NollKollTroll/PZ1_Pico/pico_sw/6502-src/ehbasic.asm

//Enhanced BASIC ver 2.22p5.7ak
// 2.00      new revision numbers start here
// 2.01      fixed LCASE$() and UCASE$()
// 2.02      new get value routine done
// 2.03      changed RND() to galoise method
// 2.04      fixed SPC()
// 2.05      new get value routine fixed
// 2.06      changed USR() code
// 2.07      fixed STR$()
// 2.08      changed INPUT and READ to remove need for $00 start to input buffer
// 2.09      fixed RND()
// 2.10      integrated missed changes from an earlier version
// 2.20      added ELSE to IF .. THEN and fixed IF .. GOTO <statement> to cause error
// 2.21      fixed IF .. THEN RETURN to not cause error
// 2.22      fixed RND() breaking the get byte routine
// 2.22p     patched to disable use of decimal mode and fix Ibuff issues
//              (bugsnquirks.txt notes 2, 4 and 5)
//              tabs converted to spaces, tabwidth=6
// 2.22p2    fixed can't continue error on 1st statement after direct mode
//              changed INPUT to throw "break in line ##" on empty line input
// 2.22p3    fixed RAM above code / Ibuff above EhBASIC patch breaks STR$()
//              fix provided by github user mgcaret
// 2.22p4    fixed string compare of equal strings in direct mode returns FALSE
//              fixed FALSE stored to a variable after a string compare
//                 is > 0 and < 1E-16
//              added additional stack floor protection for background interrupts
//              fixed conditional LOOP & NEXT cannot find their data strucure on stack
// 2.22p5    fixes issues reported by users Ruud and dclxvi on the 6502.org forum
//      5.0     http://forum.6502.org/viewtopic.php?f=5&t=5500
//              sanity check for RAM top allows values below RAM base
//      5.1-7   http://forum.6502.org/viewtopic.php?f=5&t=5606
//              1-7 coresponds to the bug# in the thread
//      5.1     TO expression with a subtract may evaluate with the sign bit flipped
//      5.3     call to LAB_1B5B may return to an address -$100 (page not incremented)
//      5.4     string concatenate followed by MINUS or NOT() crashes EhBASIC
//      5.5     garbage collection may cause an overlap with temporary strings
//      5.6     floating point multiply rounding bug
//      5.7     VAL() may cause string variables to be trashed
// 2.22p5.7ak   Adam Klotblixt: PZ1 additions and changes, jasm-fixed.

include "portdefs.asm"
include "zpos.asm"
include "oscalls.asm"

section code, "dummy filler for ROM", 0, 512
{
    define byte[512] dummy_filler = {0, ...}
}

section bss, "zeropage basic", 0, 224
{
    // zero page use
    // the following locations are bulk initialized from StrTab at LAB_GMEM
    reserve byte LAB_WARM           // BASIC warm start entry point:
    reserve byte Wrmjpl             // BASIC warm start vector jump low byte
    reserve byte Wrmjph             // BASIC warm start vector jump high byte
    reserve byte Usrjmp             // USR function jmp address
    reserve byte Usrjpl             // USR function jmp vector low byte
    reserve byte Usrjph             // USR function jmp vector high byte
    reserve byte Nullct             // nulls output after each line
    reserve byte TPos               // BASIC terminal position byte
    reserve byte TWidth             // BASIC terminal width byte
    reserve byte Iclim              // input column limit
    reserve byte Itempl             // temporary integer low byte
    reserve byte Itemph             // temporary integer high byte
    // end bulk initialize from StrTab at LAB_GMEM

    const        nums_1  = Itempl   // number to bin/hex string convert MSB
    const        nums_2  = nums_1+1 // number to bin/hex string convert
    reserve byte nums_3             // number to bin/hex string convert LSB

    reserve byte Srchc              // search character
    const        Temp3   = Srchc    // temp byte used in number routines
    reserve byte Scnquo             // scan-between-quotes flag
    const        Asrch   = Scnquo   // alt search character

    const        XOAw_l  = Srchc    // XOR, OR and AND word low byte
    const        XOAw_h  = Scnquo   // XOR, OR and AND word high byte

    reserve byte Ibptr              // input buffer pointer
    const        Dimcnt  = Ibptr    // # of dimensions
    const        Tindx   = Ibptr    // token index

    reserve byte Defdim              // default DIM flag
    reserve byte Dtypef              // data type flag, $FF=string, $00=numeric
    reserve byte Oquote              // open quote flag (b7) (Flag: DATA scan// LIST quote// memory)
    const        Gclctd  = Oquote    // garbage collected flag
    reserve byte Sufnxf              // subscript/FNX flag, 1xxx xxx = FN(0xxx xxx)
    reserve byte Imode               // input mode flag, $00=INPUT, $80=READ

    reserve byte Cflag               // comparison evaluation flag

    reserve byte TabSiz              // TAB step size (was input flag)

    reserve byte next_s              // next descriptor stack address

    // these two bytes form a word pointer to the item
    // currently on top of the descriptor stack
    reserve byte last_sl             // last descriptor stack address low byte
    reserve byte last_sh             // last descriptor stack address high byte (always $00)

    reserve byte [9] des_sk          // descriptor stack start address (temp strings)

    reserve byte ut1_pl              // utility pointer 1 low byte
    reserve byte ut1_ph              // utility pointer 1 high byte
    reserve byte ut2_pl              // utility pointer 2 low byte
    reserve byte ut2_ph              // utility pointer 2 high byte

    const        Temp_2  = ut1_pl    // temp byte for block move

    reserve byte FACt_1              // FAC temp mantissa1
    reserve byte FACt_2              // FAC temp mantissa2
    reserve byte FACt_3              // FAC temp mantissa3

    const        dims_l  = FACt_2    // array dimension size low byte
    const        dims_h  = FACt_3    // array dimension size high byte

    reserve byte TempB               // temp page 0 byte

    reserve byte Smeml               // start of mem low byte       (Start-of-Basic)
    reserve byte Smemh               // start of mem high byte      (Start-of-Basic)
    reserve byte Svarl               // start of vars low byte      (Start-of-Variables)
    reserve byte Svarh               // start of vars high byte     (Start-of-Variables)
    reserve byte Sarryl              // var mem end low byte        (Start-of-Arrays)
    reserve byte Sarryh              // var mem end high byte       (Start-of-Arrays)
    reserve byte Earryl              // array mem end low byte      (End-of-Arrays)
    reserve byte Earryh              // array mem end high byte     (End-of-Arrays)
    reserve byte Sstorl              // string storage low byte     (String storage (moving down))
    reserve byte Sstorh              // string storage high byte    (String storage (moving down))
    reserve byte Sutill              // string utility ptr low byte
    reserve byte Sutilh              // string utility ptr high byte
    reserve byte Ememl               // end of mem low byte         (Limit-of-memory)
    reserve byte Ememh               // end of mem high byte        (Limit-of-memory)
    reserve byte Clinel              // current line low byte       (Basic line number)
    reserve byte Clineh              // current line high byte      (Basic line number)
    reserve byte Blinel              // break line low byte         (Previous Basic line number)
    reserve byte Blineh              // break line high byte        (Previous Basic line number)

    reserve byte Cpntrl              // continue pointer low byte
    reserve byte Cpntrh              // continue pointer high byte

    reserve byte Dlinel              // current DATA line low byte
    reserve byte Dlineh              // current DATA line high byte

    reserve byte Dptrl               // DATA pointer low byte
    reserve byte Dptrh               // DATA pointer high byte

    reserve byte Rdptrl              // read pointer low byte
    reserve byte Rdptrh              // read pointer high byte

    reserve byte Varnm1              // current var name 1st byte
    reserve byte Varnm2              // current var name 2nd byte

    reserve byte Cvaral              // current var address low byte
    reserve byte Cvarah              // current var address high byte

    reserve byte Frnxtl              // var pointer for FOR/NEXT low byte
    reserve byte Frnxth              // var pointer for FOR/NEXT high byte

    const        Tidx1   = Frnxtl    // temp line index

    const        Lvarpl  = Frnxtl    // let var pointer low byte
    const        Lvarph  = Frnxth    // let var pointer high byte

    reserve byte [2] prstk           // precedence stacked flag

    reserve byte comp_f              // compare function flag, bits 0,1 and 2 used
                                     // bit 2 set if >
                                     // bit 1 set if =
                                     // bit 0 set if <

    reserve byte func_l              // function pointer low byte
    reserve byte func_h              // function pointer high byte

    const        garb_l  = func_l    // garbage collection working pointer low byte
    const        garb_h  = func_h    // garbage collection working pointer high byte

    reserve byte des_2l              // string descriptor_2 pointer low byte
    reserve byte des_2h              // string descriptor_2 pointer high byte

    reserve byte g_step              // garbage collect step size

    reserve byte Fnxjmp              // jump vector for functions
    reserve byte Fnxjpl              // functions jump vector low byte
    reserve byte Fnxjph              // functions jump vector high byte

    const        g_indx  = Fnxjpl    // garbage collect temp index

    const        FAC2_r  = Fnxjph    // FAC2 rounding byte

    reserve byte Adatal              // array data pointer low byte
    reserve byte Adatah              // array data pointer high  byte

    const        Nbendl  = Adatal    // new block end pointer low byte
    const        Nbendh  = Adatah    // new block end pointer high  byte

    reserve byte Obendl              // old block end pointer low byte
    reserve byte Obendh              // old block end pointer high  byte

    reserve byte numexp              // string to float number exponent count
    reserve byte expcnt              // string to float exponent count

    const        numbit  = numexp    // bit count for array element calculations

    reserve byte numdpf              // string to float decimal point flag
    reserve byte expneg              // string to float eval exponent -ve flag

    const        Astrtl  = numdpf    // array start pointer low byte
    const        Astrth  = expneg    // array start pointer high  byte

    const        Histrl  = numdpf    // highest string low byte
    const        Histrh  = expneg    // highest string high  byte

    const        Baslnl  = numdpf    // BASIC search line pointer low byte
    const        Baslnh  = expneg    // BASIC search line pointer high  byte

    const        Fvar_l  = numdpf    // find/found variable pointer low byte
    const        Fvar_h  = expneg    // find/found variable pointer high  byte

    const        Ostrtl  = numdpf    // old block start pointer low byte
    const        Ostrth  = expneg    // old block start pointer high  byte

    const        Vrschl  = numdpf    // variable search pointer low byte
    const        Vrschh  = expneg    // variable search pointer high  byte

    reserve byte FAC1_e              // FAC1 exponent

    reserve byte FAC1_1              // FAC1 mantissa1
    reserve byte FAC1_2              // FAC1 mantissa2
    reserve byte FAC1_3              // FAC1 mantissa3
    reserve byte FAC1_s              // FAC1 sign (b7)

    const        str_ln  = FAC1_e    // string length
    const        str_pl  = FAC1_1    // string pointer low byte
    const        str_ph  = FAC1_2    // string pointer high byte

    const        des_pl  = FAC1_2    // string descriptor pointer low byte
    const        des_ph  = FAC1_3    // string descriptor pointer high byte

    const        mids_l  = FAC1_3    // MID$ string temp length byte

    reserve byte negnum              // string to float eval -ve flag
    const        numcon  = negnum    // series evaluation constant count

    reserve byte FAC1_o              // FAC1 overflow byte

    reserve byte FAC2_e              // FAC2 exponent
    reserve byte FAC2_1              // FAC2 mantissa1
    reserve byte FAC2_2              // FAC2 mantissa2
    reserve byte FAC2_3              // FAC2 mantissa3
    reserve byte FAC2_s              // FAC2 sign (b7)

    reserve byte FAC_sc              // FAC sign comparison, Acc#1 vs #2
    reserve byte FAC1_r              // FAC1 rounding byte

    const        ssptr_l = FAC_sc    // string start pointer low byte
    const        ssptr_h = FAC1_r    // string start pointer high byte

    const        sdescr  = FAC_sc    // string descriptor pointer

    reserve byte Asptl               // array size/pointer low byte
    reserve byte Aspth               // array size/pointer high byte

    const        csidx   = Asptl     // line crunch save index

    const        Btmpl   = Asptl     // BASIC pointer temp low byte
    const        Btmph   = Aspth     // BASIC pointer temp low byte

    const        Cptrl   = Asptl     // BASIC pointer temp low byte
    const        Cptrh   = Aspth     // BASIC pointer temp low byte

    const        Sendl   = Asptl     // BASIC pointer temp low byte
    const        Sendh   = Aspth     // BASIC pointer temp low byte

    // the following locations are bulk initialized from LAB_2CEE at LAB_2D4E
    reserve byte [6] LAB_IGBY        // get next BASIC byte subroutine:
    reserve byte LAB_GBYT            // get current BASIC byte subroutine:
    reserve byte Bpntrl              // BASIC execute (get byte) pointer low byte
    reserve byte Bpntrh              // BASIC execute (get byte) pointer high byte
    reserve byte [19];
    // end bulk initialize from LAB_2CEE at LAB_2D4E

    reserve byte Rbyte4              // extra PRNG byte
    reserve byte Rbyte1              // most significant PRNG byte
    reserve byte Rbyte2              // middle PRNG byte
    reserve byte Rbyte3              // least significant PRNG byte

    reserve byte Decss               // number to decimal string start
    reserve byte [16] Decssp1        // number to decimal string start
    
    // Ibuffs can now be anywhere in RAM, ensure that the max length is < $80,
    // the input buffer must not cross a page boundary and must not overlap with
    // program RAM pages!
    reserve byte [65] Ibuffs         // input buffer
}

section code, "basic code", $0200, 16384
{
BASIC_begin:
    // offsets from a base of x or y
    const PLUS_0            = $00             // x or y plus 0
    const PLUS_1            = $01             // x or y plus 1
    const PLUS_2            = $02             // x or y plus 2
    const PLUS_3            = $03             // x or y plus 3

    const LAB_STAK          = $0100           // stack bottom, no offset
    const LAB_SKFE          = LAB_STAK+$FE    // flushed stack address
    const LAB_SKFF          = LAB_STAK+$FF    // flushed stack address

    const Ram_base          = BASIC_end       // start of user RAM (set as needed, should be page aligned)
    const Ram_top           = $FE00           // end of user RAM+1 (set as needed, should be page aligned)

    static_assert((Ram_base & $ff) == 0, "Ram_base not page aligned")
    static_assert((Ram_top & $ff) == 0, "Ram_top not page aligned")

    const Stack_floor       = 16              // bytes left free on stack for background interrupts

    // BASIC cold start entry point
    LAB_COLD:
          ldx   #$FF              // set byte
          stx   Clineh            // set current line high byte (set immediate mode)
          txs                     // reset stack pointer

          lda   #$4C              // code for jmp
          sta   Fnxjmp            // save for jump vector for functions

    // copy block from LAB_2CEE to $00BC - $00D7
          ldx   #StrTab-LAB_2CEE  // set byte count
    LAB_2D4E:
          lda   LAB_2CEE-1,x      // get byte from table
          sta   LAB_IGBY-1,x      // save byte in page zero
          dex                     // decrement count
          bne   LAB_2D4E          // loop if not all done

    // copy block from StrTab to $0000 - $0012
    LAB_GMEM:
          ldx   #EndTab-StrTab-1  // set byte count-1
    TabLoop:
          lda   StrTab,x          // get byte from table
          sta   LAB_WARM,x        // save byte in page zero
          dex                     // decrement count
          bpl   TabLoop           // loop if not all done

    // set-up start values
          lda   #$00              // clear a
          sta   FAC1_o            // clear FAC1 overflow byte
          sta   last_sh           // clear descriptor stack top item pointer high byte

          lda   #$08              // set default tab size
          sta   TabSiz            // save it
          lda   #$03              // set garbage collect step size for descriptor stack
          sta   g_step            // save it
          ldx   #des_sk           // descriptor stack start
          stx   next_s            // set descriptor stack pointer
          lda   #<LAB_MSZM        // point to memory size message (low addr)
          ldy   #>LAB_MSZM        // point to memory size message (high addr)
          jsr   LAB_18C3          // print null terminated string from memory

    MEM_OK:
          lda   #<Ram_top         //BASIC_begin
          ldy   #>Ram_top         //BASIC_begin

          sta   Ememl             // set end of mem low byte
          sty   Ememh             // set end of mem high byte
          sta   Sstorl            // set bottom of string space low byte
          sty   Sstorh            // set bottom of string space high byte

          ldy   #<Ram_base        // set start addr low byte
          ldx   #>Ram_base        // set start addr high byte
          sty   Smeml             // save start of mem low byte
          stx   Smemh             // save start of mem high byte

          tya                     // clear a
          sta   (Smeml),y         // clear first byte
          inc   Smeml             // increment start of mem low byte

          jsr   LAB_1463          // do "NEW" and "CLEAR"
          lda   Ememl             // get end of mem low byte
          sec                     // set carry for subtract
          sbc   Smeml             // subtract start of mem low byte
          tax                     // copy to x
          lda   Ememh             // get end of mem high byte
          sbc   Smemh             // subtract start of mem high byte
          jsr   LAB_295E          // print XA as unsigned integer (bytes free)
          lda   #<LAB_SMSG        // point to sign-on message (low addr)
          ldy   #>LAB_SMSG        // point to sign-on message (high addr)
          jsr   LAB_18C3          // print null terminated string from memory
          lda   #<LAB_COPY        // point to copyright message (low addr)
          ldy   #>LAB_COPY        // point to copyright message (high addr)
          jsr   LAB_18C3          // print null terminated string from memory
          lda   #<LAB_1274        // warm start vector low byte
          ldy   #>LAB_1274        // warm start vector high byte
          sta   Wrmjpl            // save warm start vector low byte
          sty   Wrmjph            // save warm start vector high byte
          jmp   (Wrmjpl)          // go do warm start

    // open up space in memory
    // move (Ostrtl)-(Obendl) to new block ending at (Nbendl)

    // Nbendl,Nbendh - new block end address (a/y)
    // Obendl,Obendh - old block end address
    // Ostrtl,Ostrth - old block start address

    // returns with ..

    // Nbendl,Nbendh - new block start address (high byte - $100)
    // Obendl,Obendh - old block start address (high byte - $100)
    // Ostrtl,Ostrth - old block start address (unchanged)

    LAB_11CF:
          jsr   LAB_121F          // check available memory, "Out of memory" error if no room
                                  // addr to check is in AY (low/high)
          sta   Earryl            // save new array mem end low byte
          sty   Earryh            // save new array mem end high byte

    // open up space in memory
    // move (Ostrtl)-(Obendl) to new block ending at (Nbendl)
    // don't set array end

    LAB_11D6:
          sec                     // set carry for subtract
          lda   Obendl            // get block end low byte
          sbc   Ostrtl            // subtract block start low byte
          tay                     // copy MOD(block length/$100) byte to y
          lda   Obendh            // get block end high byte
          sbc   Ostrth            // subtract block start high byte
          tax                     // copy block length high byte to x
          inx                     // +1 to allow for count=0 exit
          tya                     // copy block length low byte to a
          beq   LAB_120A          // branch if length low byte=0

                                  // block is (x-1)*256+y bytes, do the y bytes first

          sec                     // set carry for add + 1, two's complement
          eor   #$FF              // invert low byte for subtract
          adc   Obendl            // add block end low byte

          sta   Obendl            // save corrected old block end low byte
          bcs   LAB_11F3          // branch if no underflow

          dec   Obendh            // else decrement block end high byte
          sec                     // set carry for add + 1, two's complement
    LAB_11F3:
          tya                     // get MOD(block length/$100) byte
          eor   #$FF              // invert low byte for subtract
          adc   Nbendl            // add destination end low byte
          sta   Nbendl            // save modified new block end low byte
          bcs   LAB_1203          // branch if no underflow

          dec   Nbendh            // else decrement block end high byte
          bcc   LAB_1203          // branch always

    LAB_11FF:
          lda   (Obendl),y        // get byte from source
          sta   (Nbendl),y        // copy byte to destination
    LAB_1203:
          dey                     // decrement index
          bne   LAB_11FF          // loop until y=0

                                  // now do y=0 indexed byte
          lda   (Obendl),y        // get byte from source
          sta   (Nbendl),y        // save byte to destination
    LAB_120A:
          dec   Obendh            // decrement source pointer high byte
          dec   Nbendh            // decrement destination pointer high byte
          dex                     // decrement block count
          bne   LAB_1203          // loop until count = $0

          rts

    // check room on stack for a bytes
    // stack too deep? do OM error

    LAB_1212:
    // *** patch - additional stack floor protection for background interrupts
    // *** add
          if (Stack_floor != 0)
          {
              clc                     // prep adc
              adc   #Stack_floor      // stack pointer lower limit before interrupts
          }
    // *** end patch
          sta   TempB             // save result in temp byte
          tsx                     // copy stack
          cpx   TempB             // compare new "limit" with stack
          bcc   LAB_OMER          // if stack < limit do "Out of memory" error then warm start

          rts

    // check available memory, "Out of memory" error if no room
    // addr to check is in AY (low/high)

    LAB_121F:
          cpy   Sstorh            // compare bottom of string mem high byte
          bcc   LAB_124B          // if less then exit (is ok)

          bne   LAB_1229          // skip next test if greater (tested <)

                                  // high byte was =, now do low byte
          cmp   Sstorl            // compare with bottom of string mem low byte
          bcc   LAB_124B          // if less then exit (is ok)

                                  // addr is > string storage ptr (oops!)
    LAB_1229:
          pha                     // push addr low byte
          ldx   #$08              // set index to save Adatal to expneg inclusive
          tya                     // copy addr high byte (to push on stack)

                                  // save misc numeric work area
    LAB_122D:
          pha                     // push byte
          lda   Adatal-1,x        // get byte from Adatal to expneg ( ,$00 not pushed)
          dex                     // decrement index
          bpl   LAB_122D          // loop until all done

          jsr   LAB_GARB          // garbage collection routine

                                  // restore misc numeric work area
          ldx   #$00              // clear the index to restore bytes
    LAB_1238:
          pla                     // pop byte
          sta   Adatal,x          // save byte to Adatal to expneg
          inx                     // increment index
          cpx   #$08              // compare with end + 1
          bmi   LAB_1238          // loop if more to do

          pla                     // pop addr high byte
          tay                     // copy back to y
          pla                     // pop addr low byte
          cpy   Sstorh            // compare bottom of string mem high byte
          bcc   LAB_124B          // if less then exit (is ok)

          bne   LAB_OMER          // if greater do "Out of memory" error then warm start

                                  // high byte was =, now do low byte
          cmp   Sstorl            // compare with bottom of string mem low byte
          bcs   LAB_OMER          // if >= do "Out of memory" error then warm start

                                  // ok exit, carry clear
    LAB_124B:
          rts

    // do "Out of memory" error then warm start

    LAB_OMER:
          ldx   #$0C              // error code $0C ("Out of memory" error)

    // do error #x, then warm start

    LAB_XERR:
          jsr   LAB_CRLF          // print CR/LF

          lda   LAB_BAER,x        // get error message pointer low byte
          ldy   LAB_BAER+1,x      // get error message pointer high byte
          jsr   LAB_18C3          // print null terminated string from memory

          jsr   LAB_1491          // flush stack and clear continue flag
          lda   #<LAB_EMSG        // point to " Error" low addr
          ldy   #>LAB_EMSG        // point to " Error" high addr
    LAB_1269:
          jsr   LAB_18C3          // print null terminated string from memory
          ldy   Clineh            // get current line high byte
          iny                     // increment it
          beq   LAB_1274          // go do warm start (was immediate mode)

                                  // else print line number
          jsr   LAB_2953          // print " in line [LINE #]"

    // BASIC warm start entry point
    // wait for Basic command

    LAB_1274:
          lda   #<LAB_RMSG        // point to "Ready" message low byte
          ldy   #>LAB_RMSG        // point to "Ready" message high byte

          jsr   LAB_18C3          // go do print string

    // wait for Basic command (no "Ready")

    LAB_127D:
          jsr   LAB_1357          // call for BASIC input
    LAB_1280:
          stx   Bpntrl            // set BASIC execute pointer low byte
          sty   Bpntrh            // set BASIC execute pointer high byte
          jsr   LAB_GBYT          // scan memory
          beq   LAB_127D          // loop while null

    // got to interpret input line now ..

          ldx   #$FF              // current line to null value
          stx   Clineh            // set current line high byte
          bcc   LAB_1295          // branch if numeric character (handle new BASIC line)

                                  // no line number .. immediate mode
          jsr   LAB_13A6          // crunch keywords into Basic tokens
          jmp   LAB_15F6          // go scan and interpret code

    // handle new BASIC line

    LAB_1295:
          jsr   LAB_GFPN          // get fixed-point number into temp integer
          jsr   LAB_13A6          // crunch keywords into Basic tokens
          sty   Ibptr             // save index pointer to end of crunched line
          jsr   LAB_SSLN          // search BASIC for temp integer line number
          bcc   LAB_12E6          // branch if not found

                                  // aroooogah! line # already exists! delete it
          ldy   #$01              // set index to next line pointer high byte
          lda   (Baslnl),y        // get next line pointer high byte
          sta   ut1_ph            // save it
          lda   Svarl             // get start of vars low byte
          sta   ut1_pl            // save it
          lda   Baslnh            // get found line pointer high byte
          sta   ut2_ph            // save it
          lda   Baslnl            // get found line pointer low byte
          dey                     // decrement index
          sbc   (Baslnl),y        // subtract next line pointer low byte
          clc                     // clear carry for add
          adc   Svarl             // add start of vars low byte
          sta   Svarl             // save new start of vars low byte
          sta   ut2_pl            // save destination pointer low byte
          lda   Svarh             // get start of vars high byte
          adc   #$FF              // -1 + carry
          sta   Svarh             // save start of vars high byte
          sbc   Baslnh            // subtract found line pointer high byte
          tax                     // copy to block count
          sec                     // set carry for subtract
          lda   Baslnl            // get found line pointer low byte
          sbc   Svarl             // subtract start of vars low byte
          tay                     // copy to bytes in first block count
          bcs   LAB_12D0          // branch if overflow

          inx                     // increment block count (correct for =0 loop exit)
          dec   ut2_ph            // decrement destination high byte
    LAB_12D0:
          clc                     // clear carry for add
          adc   ut1_pl            // add source pointer low byte
          bcc   LAB_12D8          // branch if no overflow

          dec   ut1_ph            // else decrement source pointer high byte
          clc                     // clear carry

                                  // close up memory to delete old line
    LAB_12D8:
          lda   (ut1_pl),y        // get byte from source
          sta   (ut2_pl),y        // copy to destination
          iny                     // increment index
          bne   LAB_12D8          // while <> 0 do this block

          inc   ut1_ph            // increment source pointer high byte
          inc   ut2_ph            // increment destination pointer high byte
          dex                     // decrement block count
          bne   LAB_12D8          // loop until all done

                                  // got new line in buffer and no existing same #
    LAB_12E6:
          lda   Ibuffs            // get byte from start of input buffer
          beq   LAB_1319          // if null line just go flush stack/vars and exit

                                  // got new line and it isn't empty line
          lda   Ememl             // get end of mem low byte
          ldy   Ememh             // get end of mem high byte
          sta   Sstorl            // set bottom of string space low byte
          sty   Sstorh            // set bottom of string space high byte
          lda   Svarl             // get start of vars low byte  (end of BASIC)
          sta   Obendl            // save old block end low byte
          ldy   Svarh             // get start of vars high byte (end of BASIC)
          sty   Obendh            // save old block end high byte
          adc   Ibptr             // add input buffer pointer    (also buffer length)
          bcc   LAB_1301          // branch if no overflow from add

          iny                     // else increment high byte
    LAB_1301:
          sta   Nbendl            // save new block end low byte (move to, low byte)
          sty   Nbendh            // save new block end high byte
          jsr   LAB_11CF          // open up space in memory
                                  // old start pointer Ostrtl,Ostrth set by the find line call
          lda   Earryl            // get array mem end low byte
          ldy   Earryh            // get array mem end high byte
          sta   Svarl             // save start of vars low byte
          sty   Svarh             // save start of vars high byte
          ldy   Ibptr             // get input buffer pointer    (also buffer length)
          dey                     // adjust for loop type
    LAB_1311:
          lda   Ibuffs-4,y        // get byte from crunched line
          sta   (Baslnl),y        // save it to program memory
          dey                     // decrement count
          cpy   #$03              // compare with first byte-1
          bne   LAB_1311          // continue while count <> 3

          lda   Itemph            // get line # high byte
          sta   (Baslnl),y        // save it to program memory
          dey                     // decrement count
          lda   Itempl            // get line # low byte
          sta   (Baslnl),y        // save it to program memory
          dey                     // decrement count
          lda   #$FF              // set byte to allow chain rebuild. if you didn't set this
                                  // byte then a zero already here would stop the chain rebuild
                                  // as it would think it was the [EOT] marker.
          sta   (Baslnl),y        // save it to program memory

    LAB_1319:
          jsr   LAB_1477          // reset execution to start, clear vars and flush stack
          ldx   Smeml             // get start of mem low byte
          lda   Smemh             // get start of mem high byte
          ldy   #$01              // index to high byte of next line pointer
    LAB_1325:
          stx   ut1_pl            // set line start pointer low byte
          sta   ut1_ph            // set line start pointer high byte
          lda   (ut1_pl),y        // get it
          beq   LAB_133E          // exit if end of program

    // rebuild chaining of Basic lines

          ldy   #$04              // point to first code byte of line
                                  // there is always 1 byte + [EOL] as null entries are deleted
    LAB_1330:
          iny                     // next code byte
          lda   (ut1_pl),y        // get byte
          bne   LAB_1330          // loop if not [EOL]

          sec                     // set carry for add + 1
          tya                     // copy end index
          adc   ut1_pl            // add to line start pointer low byte
          tax                     // copy to x
          ldy   #$00              // clear index, point to this line's next line pointer
          sta   (ut1_pl),y        // set next line pointer low byte
          tya                     // clear a
          adc   ut1_ph            // add line start pointer high byte + carry
          iny                     // increment index to high byte
          sta   (ut1_pl),y        // save next line pointer low byte
          bcc   LAB_1325          // go do next line, branch always, carry clear


    LAB_133E:
          jmp   LAB_127D          // else we just wait for Basic command, no "Ready"

    // print "? " and get BASIC input

    LAB_INLN:
          jsr   LAB_18E3          // print "?" character
          jsr   LAB_18E0          // print " "
          bne   LAB_1357          // call for BASIC input and return

    // receive line from keyboard

                                  // $08 as delete key (BACKSPACE on standard keyboard)
    LAB_134B:
          jsr   LAB_PRNA          // go print the character
          dex                     // decrement the buffer counter (delete)
          define byte = $2C       // make ldx into bit abs

    // call for BASIC input (main entry point)

    LAB_1357:
          ldx   #$00              // clear BASIC line buffer pointer
    LAB_1359:
          jsr   V_INPT            // call scan input device
          bcc   LAB_1359          // loop if no byte

          beq   LAB_1359          // loop until valid input (ignore NULLs)
    
          cmp   #$07              // compare with [BELL]
          beq   LAB_1378          // branch if [BELL]

          cmp   #$0D              // compare with [CR]
          beq   LAB_1384          // do CR/LF exit if [CR]

          cpx   #$00              // compare pointer with $00
          bne   LAB_1374          // branch if not empty

    // next two lines ignore any non print character and [SPACE] if input buffer empty

          cmp   #$21              // compare with [SP]+1
          bcc   LAB_1359          // if < ignore character

    LAB_1374:
          cmp   #$08              // compare with [BACKSPACE] (delete last character)
          beq   LAB_134B          // go delete last character

    LAB_1378:
          cpx   #sizeof(Ibuffs)   // compare character count with max
          bcs   LAB_138E          // skip store and do [BELL] if buffer full

          sta   Ibuffs,x          // else store in buffer
          inx                     // increment pointer
    LAB_137F:
          jsr   LAB_PRNA          // go print the character
          bne   LAB_1359          // always loop for next character

    LAB_1384:
          jmp   LAB_1866          // do CR/LF exit to BASIC

    // announce buffer full

    LAB_138E:
          lda   #$07              // [BELL] character into a
          bne   LAB_137F          // go print the [BELL] but ignore input character
                                  // branch always

    // crunch keywords into Basic tokens
    // position independent buffer version ..
    // faster, dictionary search version ....

    LAB_13A6:
          ldy   #$FF              // set save index (makes for easy math later)

          sec                     // set carry for subtract
          lda   Bpntrl            // get basic execute pointer low byte
          sbc   #<Ibuffs          // subtract input buffer start pointer
          tax                     // copy result to x (index past line # if any)

          stx   Oquote            // clear open quote/DATA flag
    LAB_13AC:
          lda   Ibuffs,x          // get byte from input buffer
          beq   LAB_13EC          // if null save byte then exit
// *** patch
          cmp   #'{'              // convert lower to upper case
          bcs   LAB_13EC          // is above lower case
          cmp   #'a'
          bcc   PATCH_LC          // is below lower case
          and   #$DF              // mask lower case bit      
    PATCH_LC:
// *** end
          cmp   #'_'              // compare with "_"
          bcs   LAB_13EC          // if >= go save byte then continue crunching

          cmp   #'<'              // compare with "<"
          bcs   LAB_13CC          // if >= go crunch now

          cmp   #'0'              // compare with "0"
          bcs   LAB_13EC          // if >= go save byte then continue crunching

          sta   Scnquo            // save buffer byte as search character
          cmp   #$22              // is it quote character?
          beq   LAB_1410          // branch if so (copy quoted string)

          cmp   #'*'              // compare with "*"
          bcc   LAB_13EC          // if < go save byte then continue crunching

                                  // else crunch now
    LAB_13CC:
          bit   Oquote            // get open quote/DATA token flag
          bvs   LAB_13EC          // branch if b6 of Oquote set (was DATA)
                                  // go save byte then continue crunching

          stx   TempB             // save buffer read index
          sty   csidx             // copy buffer save index
          ldy   #<TAB_1STC        // get keyword first character table low address
          sty   ut2_pl            // save pointer low byte
          ldy   #>TAB_1STC        // get keyword first character table high address
          sty   ut2_ph            // save pointer high byte
          ldy   #$00              // clear table pointer

    LAB_13D0:
          cmp   (ut2_pl),y        // compare with keyword first character table byte
          beq   LAB_13D1          // go do word_table_chr if match

//          bcc   LAB_13EA          // if < keyword first character table byte go restore
// *** patch
          bcc   PATCH_LC2          // if < keyword first character table byte go restore
// *** end    
                                  // y and save to crunched

          iny                     // else increment pointer
          bne   LAB_13D0          // and loop (branch always)

    // have matched first character of some keyword

    LAB_13D1:
          tya                     // copy matching index
          asl                     // *2 (bytes per pointer)
          tax                     // copy to new index
          lda   TAB_CHRT,x        // get keyword table pointer low byte
          sta   ut2_pl            // save pointer low byte
          lda   TAB_CHRT+1,x      // get keyword table pointer high byte
          sta   ut2_ph            // save pointer high byte

          ldy   #$FF              // clear table pointer (make -1 for start)

          ldx   TempB             // restore buffer read index

    LAB_13D6:
          iny                     // next table byte
          lda   (ut2_pl),y        // get byte from table
    LAB_13D8:
          bmi   LAB_13EA          // all bytes matched so go save token

          inx                     // next buffer byte
//          cmp   Ibuffs,x          // compare with byte from input buffer
// *** patch
          eor     Ibuffs,x        // check bits against table
          and     #$DF            // DF masks the upper/lower case bit
// *** end    
          beq   LAB_13D6          // go compare next if match

          bne   LAB_1417          // branch if >< (not found keyword)

    LAB_13EA:
          ldy   csidx             // restore save index

                                  // save crunched to output
    LAB_13EC:
          inx                     // increment buffer index (to next input byte)
          iny                     // increment save index (to next output byte)
          sta   Ibuffs,y          // save byte to output
          cmp   #$00              // set the flags, set carry
          beq   LAB_142A          // do exit if was null [EOL]

                                  // a holds token or byte here
          sbc   #':'              // subtract ":" (carry set by cmp #00)
          beq   LAB_13FF          // branch if it was ":" (is now $00)

                                  // a now holds token-$3A
          cmp   #TK_DATA-$3A      // compare with DATA token - $3A
          bne   LAB_1401          // branch if not DATA

                                  // token was : or DATA
    LAB_13FF:
          sta   Oquote            // save token-$3A (clear for ":", TK_DATA-$3A for DATA)
    LAB_1401:
          eor   #TK_REM-$3A       // effectively subtract REM token offset
          bne   LAB_13AC          // If wasn't REM then go crunch rest of line

          sta   Asrch             // else was REM so set search for [EOL]

                                  // loop for REM, "..." etc.
    LAB_1408:
          lda   Ibuffs,x          // get byte from input buffer
          beq   LAB_13EC          // branch if null [EOL]

          cmp   Asrch             // compare with stored character
          beq   LAB_13EC          // branch if match (end quote)

                                  // entry for copy string in quotes, don't crunch
    LAB_1410:
          iny                     // increment buffer save index
          sta   Ibuffs,y          // save byte to output
          inx                     // increment buffer read index
          bne   LAB_1408          // loop while <> 0 (should never be 0!)

                                  // not found keyword this go
    LAB_1417:
          ldx   TempB             // compare has failed, restore buffer index (start byte!)

                                  // now find the end of this word in the table
    LAB_141B:
          lda   (ut2_pl),y        // get table byte
          php                     // save status
          iny                     // increment table index
          plp                     // restore byte status
          bpl   LAB_141B          // if not end of keyword go do next

          lda   (ut2_pl),y        // get byte from keyword table
          bne   LAB_13D8          // go test next word if not zero byte (end of table)

                                  // reached end of table with no match
// *** patch
    PATCH_LC2:
// *** end                                  
          lda   Ibuffs,x          // restore byte from input buffer
          bpl   LAB_13EA          // branch always (all bytes in buffer are $00-$7F)
                                  // go save byte in output and continue crunching

                                  // reached [EOL]
    LAB_142A:
          iny                     // increment pointer
          iny                     // increment pointer (makes it next line pointer high byte)
          sta   Ibuffs,y          // save [EOL] (marks [EOT] in immediate mode)
          iny                     // adjust for line copy
          iny                     // adjust for line copy
          iny                     // adjust for line copy
    // *** begin patch for when Ibuffs is $xx00 - Daryl Rictor ***
    // *** insert
          if (Ibuffs & $FF == 0)
          {
              lda   Bpntrl            // test for $00
              bne   LAB_142P          // not $00
              dec   Bpntrh            // allow for increment when $xx00
          LAB_142P:
          }
    // *** end   patch for when Ibuffs is $xx00 - Daryl Rictor ***
    // end of patch
          dec   Bpntrl            // allow for increment
          rts

    // search Basic for temp integer line number from start of mem

    LAB_SSLN:
          lda   Smeml             // get start of mem low byte
          ldx   Smemh             // get start of mem high byte

    // search Basic for temp integer line number from AX
    // returns carry set if found
    // returns Baslnl/Baslnh pointer to found or next higher (not found) line

    // old 541 new 507

    LAB_SHLN:
          ldy   #$01              // set index
          sta   Baslnl            // save low byte as current
          stx   Baslnh            // save high byte as current
          lda   (Baslnl),y        // get pointer high byte from addr
          beq   LAB_145F          // pointer was zero so we're done, do 'not found' exit

          ldy   #$03              // set index to line # high byte
          lda   (Baslnl),y        // get line # high byte
          dey                     // decrement index (point to low byte)
          cmp   Itemph            // compare with temporary integer high byte
          bne   LAB_1455          // if <> skip low byte check

          lda   (Baslnl),y        // get line # low byte
          cmp   Itempl            // compare with temporary integer low byte
    LAB_1455:
          bcs   LAB_145E          // else if temp < this line, exit (passed line#)

    LAB_1456:
          dey                     // decrement index to next line ptr high byte
          lda   (Baslnl),y        // get next line pointer high byte
          tax                     // copy to x
          dey                     // decrement index to next line ptr low byte
          lda   (Baslnl),y        // get next line pointer low byte
          bcc   LAB_SHLN          // go search for line # in temp (Itempl/Itemph) from AX
                                  // (carry always clear)

    LAB_145E:
          beq   LAB_1460          // exit if temp = found line #, carry is set

    LAB_145F:
          clc                     // clear found flag
    LAB_1460:
          rts

    // perform NEW

    LAB_NEW:
          bne   LAB_1460          // exit if not end of statement (to do syntax error)

    LAB_1463:
          lda   #$00              // clear a
          tay                     // clear y
          sta   (Smeml),y         // clear first line, next line pointer, low byte
          iny                     // increment index
          sta   (Smeml),y         // clear first line, next line pointer, high byte
          clc                     // clear carry
          lda   Smeml             // get start of mem low byte
          adc   #$02              // calculate end of BASIC low byte
          sta   Svarl             // save start of vars low byte
          lda   Smemh             // get start of mem high byte
          adc   #$00              // add any carry
          sta   Svarh             // save start of vars high byte

    // reset execution to start, clear vars and flush stack

    LAB_1477:
          clc                     // clear carry
          lda   Smeml             // get start of mem low byte
          adc   #$FF              // -1
          sta   Bpntrl            // save BASIC execute pointer low byte
          lda   Smemh             // get start of mem high byte
          adc   #$FF              // -1+carry
          sta   Bpntrh            // save BASIC execute pointer high byte

    // "CLEAR" command gets here

    LAB_147A:
          lda   Ememl             // get end of mem low byte
          ldy   Ememh             // get end of mem high byte
          sta   Sstorl            // set bottom of string space low byte
          sty   Sstorh            // set bottom of string space high byte
          lda   Svarl             // get start of vars low byte
          ldy   Svarh             // get start of vars high byte
          sta   Sarryl            // save var mem end low byte
          sty   Sarryh            // save var mem end high byte
          sta   Earryl            // save array mem end low byte
          sty   Earryh            // save array mem end high byte
          jsr   LAB_161A          // perform RESTORE command

    // flush stack and clear continue flag

    LAB_1491:
          ldx   #des_sk           // set descriptor stack pointer
          stx   next_s            // save descriptor stack pointer
          pla                     // pull return address low byte
          tax                     // copy return address low byte
          pla                     // pull return address high byte
          stx   LAB_SKFE          // save to cleared stack
          sta   LAB_SKFF          // save to cleared stack
          ldx   #$FD              // new stack pointer
          txs                     // reset stack
          lda   #$00              // clear byte
    //*** fix p2: no longer necessary as the continue pointer is saved anyway
    //      sta   Cpntrh            // clear continue pointer high byte
          sta   Sufnxf            // clear subscript/FNX flag
    LAB_14A6:
          rts

    // perform CLEAR

    LAB_CLEAR:
          beq   LAB_147A          // if no following token go do "CLEAR"

                                  // else there was a following token (go do syntax error)
          rts

    // perform LIST [n][-m]
    // bigger, faster version (a _lot_ faster)

    LAB_LIST:
          bcc   LAB_14BD          // branch if next character numeric (LIST n..)

          beq   LAB_14BD          // branch if next character [NULL] (LIST)

          cmp   #TK_MINUS         // compare with token for -
          bne   LAB_14A6          // exit if not - (LIST -m)

                                  // LIST [[n][-m]]
                                  // this bit sets the n , if present, as the start and end
    LAB_14BD:
          jsr   LAB_GFPN          // get fixed-point number into temp integer
          jsr   LAB_SSLN          // search BASIC for temp integer line number
                                  // (pointer in Baslnl/Baslnh)
          jsr   LAB_GBYT          // scan memory
          beq   LAB_14D4          // branch if no more characters

                                  // this bit checks the - is present
          cmp   #TK_MINUS         // compare with token for -
          bne   LAB_1460          // return if not "-" (will be Syntax error)

                                  // LIST [n]-m
                                  // the - was there so set m as the end value
          jsr   LAB_IGBY          // increment and scan memory
          jsr   LAB_GFPN          // get fixed-point number into temp integer
          bne   LAB_1460          // exit if not ok

    LAB_14D4:
          lda   Itempl            // get temporary integer low byte
          ora   Itemph            // OR temporary integer high byte
          bne   LAB_14E2          // branch if start set

          lda   #$FF              // set for -1
          sta   Itempl            // set temporary integer low byte
          sta   Itemph            // set temporary integer high byte
    LAB_14E2:
          ldy   #$01              // set index for line
          sty   Oquote            // clear open quote flag
          jsr   LAB_CRLF          // print CR/LF
          lda   (Baslnl),y        // get next line pointer high byte
                                  // pointer initially set by search at LAB_14BD
          beq   LAB_152B          // if null all done so exit
          jsr   LAB_1629          // do CRTL-C check vector

          iny                     // increment index for line
          lda   (Baslnl),y        // get line # low byte
          tax                     // copy to x
          iny                     // increment index
          lda   (Baslnl),y        // get line # high byte
          cmp   Itemph            // compare with temporary integer high byte
          bne   LAB_14FF          // branch if no high byte match

          cpx   Itempl            // compare with temporary integer low byte
          beq   LAB_1501          // branch if = last line to do (< will pass next branch)

    LAB_14FF:                     // else ..:
          bcs   LAB_152B          // if greater all done so exit

    LAB_1501:
          sty   Tidx1             // save index for line
          jsr   LAB_295E          // print XA as unsigned integer
          lda   #$20              // space is the next character
    LAB_1508:
          ldy   Tidx1             // get index for line
          and   #$7F              // mask top out bit of character
    LAB_150C:
          jsr   LAB_PRNA          // go print the character
          cmp   #$22              // was it " character
          bne   LAB_1519          // branch if not

                                  // we are either entering or leaving a pair of quotes
          lda   Oquote            // get open quote flag
          eor   #$FF              // toggle it
          sta   Oquote            // save it back
    LAB_1519:
          iny                     // increment index
          lda   (Baslnl),y        // get next byte
          bne   LAB_152E          // branch if not [EOL] (go print character)
          tay                     // else clear index
          lda   (Baslnl),y        // get next line pointer low byte
          tax                     // copy to x
          iny                     // increment index
          lda   (Baslnl),y        // get next line pointer high byte
          stx   Baslnl            // set pointer to line low byte
          sta   Baslnh            // set pointer to line high byte
          bne   LAB_14E2          // go do next line if not [EOT]
                                  // else ..
    LAB_152B:
          rts

    LAB_152E:
          bpl   LAB_150C          // just go print it if not token byte

                                  // else was token byte so uncrunch it (maybe)
          bit   Oquote            // test the open quote flag
          bmi   LAB_150C          // just go print character if open quote set

          ldx   #>LAB_KEYT        // get table address high byte
          asl                     // *2
          asl                     // *4
          bcc   LAB_152F          // branch if no carry

          inx                     // else increment high byte
          clc                     // clear carry for add
    LAB_152F:
          adc   #<LAB_KEYT        // add low byte
          bcc   LAB_1530          // branch if no carry

          inx                     // else increment high byte
    LAB_1530:
          sta   ut2_pl            // save table pointer low byte
          stx   ut2_ph            // save table pointer high byte
          sty   Tidx1             // save index for line
          ldy   #$00              // clear index
          lda   (ut2_pl),y        // get length
          tax                     // copy length
          iny                     // increment index
          lda   (ut2_pl),y        // get 1st character
          dex                     // decrement length
          beq   LAB_1508          // if no more characters exit and print

          jsr   LAB_PRNA          // go print the character
          iny                     // increment index
          lda   (ut2_pl),y        // get keyword address low byte
          pha                     // save it for now
          iny                     // increment index
          lda   (ut2_pl),y        // get keyword address high byte
          ldy   #$00
          sta   ut2_ph            // save keyword pointer high byte
          pla                     // pull low byte
          sta   ut2_pl            // save keyword pointer low byte
    LAB_1540:
          lda   (ut2_pl),y        // get character
          dex                     // decrement character count
          beq   LAB_1508          // if last character exit and print

          jsr   LAB_PRNA          // go print the character
          iny                     // increment index
          bne   LAB_1540          // loop for next character

    // perform FOR

    LAB_FOR:
          lda   #$80              // set FNX
          sta   Sufnxf            // set subscript/FNX flag
          jsr   LAB_LET           // go do LET
          pla                     // pull return address
          pla                     // pull return address
          lda   #$10              // we need 16d bytes !
          jsr   LAB_1212          // check room on stack for a bytes
          jsr   LAB_SNBS          // scan for next BASIC statement ([:] or [EOL])
          clc                     // clear carry for add
          tya                     // copy index to a
          adc   Bpntrl            // add BASIC execute pointer low byte
          pha                     // push onto stack
          lda   Bpntrh            // get BASIC execute pointer high byte
          adc   #$00              // add carry
          pha                     // push onto stack
          lda   Clineh            // get current line high byte
          pha                     // push onto stack
          lda   Clinel            // get current line low byte
          pha                     // push onto stack
          lda   #TK_TO            // get "TO" token
          jsr   LAB_SCCA          // scan for CHR$(a) , else do syntax error then warm start
          jsr   LAB_CTNM          // check if source is numeric, else do type mismatch
          jsr   LAB_EVNM          // evaluate expression and check is numeric,
                                  // else do type mismatch
    // *** begin patch  2.22p5.1   TO expression may get sign bit flipped
    // *** add
          jsr   LAB_27BA          // round FAC1
    // *** end   patch  2.22p5.1   TO expression may get sign bit flipped
          lda   FAC1_s            // get FAC1 sign (b7)
          ora   #$7F              // set all non sign bits
          and   FAC1_1            // and FAC1 mantissa1
          sta   FAC1_1            // save FAC1 mantissa1
          lda   #<LAB_159F        // set return address low byte
          ldy   #>LAB_159F        // set return address high byte
          sta   ut1_pl            // save return address low byte
          sty   ut1_ph            // save return address high byte
          jmp   LAB_1B66          // round FAC1 and put on stack (returns to next instruction)

    LAB_159F:
          lda   #<LAB_259C        // set 1 pointer low addr (default step size)
          ldy   #>LAB_259C        // set 1 pointer high addr
          jsr   LAB_UFAC          // unpack memory (AY) into FAC1
          jsr   LAB_GBYT          // scan memory
          cmp   #TK_STEP          // compare with STEP token
          bne   LAB_15B3          // jump if not "STEP"

                                  //.was step so ..
          jsr   LAB_IGBY          // increment and scan memory
          jsr   LAB_EVNM          // evaluate expression and check is numeric,
                                  // else do type mismatch
    LAB_15B3:
          jsr   LAB_27CA          // return a=FF,C=1/-ve a=01,C=0/+ve
          sta   FAC1_s            // set FAC1 sign (b7)
                                  // this is +1 for +ve step and -1 for -ve step, in NEXT we
                                  // compare the FOR value and the TO value and return +1 if
                                  // FOR > TO, 0 if FOR = TO and -1 if FOR < TO. the value
                                  // here (+/-1) is then compared to that result and if they
                                  // are the same (+ve and FOR > TO or -ve and FOR < TO) then
                                  // the loop is done

    // *** begin patch  2.22p5.3   potential return address -$100 (page not incremented) ***
    // *** add
       if ((* & $FF) == $FD)
       {
           nop                     // return address of jsr +1 (on  next page)
       }
    // *** end   patch  2.22p5.3   potential return address -$100 (page not incremented) ***
          jsr   LAB_1B5B          // push sign, round FAC1 and put on stack
          lda   Frnxth            // get var pointer for FOR/NEXT high byte
          pha                     // push on stack
          lda   Frnxtl            // get var pointer for FOR/NEXT low byte
          pha                     // push on stack
          lda   #TK_FOR           // get FOR token
          pha                     // push on stack

    // interpreter inner loop

    LAB_15C2:
          jsr   LAB_1629          // do CRTL-C check vector
          lda   Bpntrl            // get BASIC execute pointer low byte
          ldy   Bpntrh            // get BASIC execute pointer high byte

          ldx   Clineh            // continue line is $FFxx for immediate mode
                                  // ($00xx for RUN from immediate mode)
          inx                     // increment it (now $00 if immediate mode)
    //*** fix p2: skip no longer necessary as the continue pointer is saved anyway
    //      beq   LAB_15D1          // branch if null (immediate mode)

          sta   Cpntrl            // save continue pointer low byte
          sty   Cpntrh            // save continue pointer high byte
    LAB_15D1:
          ldy   #$00              // clear index
          lda   (Bpntrl),y        // get next byte
          beq   LAB_15DC          // branch if null [EOL]

          cmp   #':'              // compare with ":"
          beq   LAB_15F6          // branch if = (statement separator)

    LAB_15D9:
          jmp   LAB_SNER          // else syntax error then warm start

                                  // have reached [EOL]
    LAB_15DC:
          ldy   #$02              // set index
          lda   (Bpntrl),y        // get next line pointer high byte
          clc                     // clear carry for no "BREAK" message
          beq   LAB_1651          // if null go to immediate mode (was immediate or [EOT]
                                  // marker)

          iny                     // increment index
          lda   (Bpntrl),y        // get line # low byte
          sta   Clinel            // save current line low byte
          iny                     // increment index
          lda   (Bpntrl),y        // get line # high byte
          sta   Clineh            // save current line high byte
          tya                     // a now = 4
          adc   Bpntrl            // add BASIC execute pointer low byte
          sta   Bpntrl            // save BASIC execute pointer low byte
          bcc   LAB_15F6          // branch if no overflow

          inc   Bpntrh            // else increment BASIC execute pointer high byte
    LAB_15F6:
          jsr   LAB_IGBY          // increment and scan memory

    LAB_15F9:
          jsr   LAB_15FF          // go interpret BASIC code from (Bpntrl)

    LAB_15FC:
          jmp   LAB_15C2          // loop

    // interpret BASIC code from (Bpntrl)

    LAB_15FF:
          beq   LAB_1628          // exit if zero [EOL]

    LAB_1602:
          asl                     // *2 bytes per vector and normalise token
          bcs   LAB_1609          // branch if was token

          jmp   LAB_LET           // else go do implied LET

    LAB_1609:
          cmp   #(TK_TAB - $80) * 2 // compare normalised token * 2 with TAB
          bcs   LAB_15D9          // branch if a>=TAB (do syntax error then warm start)
                                  // only tokens before TAB can start a line
          tay                     // copy to index
          lda   LAB_CTBL+1,y      // get vector high byte
          pha                     // onto stack
          lda   LAB_CTBL,y        // get vector low byte
          pha                     // onto stack
          jmp   LAB_IGBY          // jump to increment and scan memory
                                  // then "return" to vector

    // CTRL-C check jump. this is called as a subroutine but exits back via a jump if a
    // key press is detected.

    LAB_1629:
          jmp   CTRLC             // ctrl c check vector

    // if there was a key press it gets back here ..

    LAB_1636:
          cmp   #$03              // compare with CTRL-C
          
    // perform STOP
    LAB_STOP:
          bcs   LAB_163B          // branch if token follows STOP
                                  // else just END
    // END
    LAB_END:
          clc                     // clear the carry, indicate a normal program end
    LAB_163B:
          bne   LAB_167A          // if wasn't CTRL-C or there is a following byte return

          lda   Bpntrh            // get the BASIC execute pointer high byte
    //*** fix p2: skip no longer necessary as the continue pointer is saved anyway
    //      eor   #>Ibuffs          // compare with buffer address high byte (Cb unchanged)
    //      beq   LAB_164F          // branch if the BASIC pointer is in the input buffer
    //                              // (can't continue in immediate mode)
    //                              // else ..
    //      eor   #>Ibuffs          // correct the bits
          ldy   Bpntrl            // get BASIC execute pointer low byte
          sty   Cpntrl            // save continue pointer low byte
          sta   Cpntrh            // save continue pointer high byte
    LAB_1647:
          lda   Clinel            // get current line low byte
          ldy   Clineh            // get current line high byte
          sta   Blinel            // save break line low byte
          sty   Blineh            // save break line high byte
    LAB_164F:
          pla                     // pull return address low
          pla                     // pull return address high
    LAB_1651:
          bcc   LAB_165E          // if was program end just do warm start

                                  // else ..
          lda   #<LAB_BMSG        // point to "Break" low byte
          ldy   #>LAB_BMSG        // point to "Break" high byte
          jmp   LAB_1269          // print "Break" and do warm start

    LAB_165E:
          jmp   LAB_1274          // go do warm start

    // perform RESTORE

    LAB_RESTORE:
          bne   LAB_RESTOREn      // branch if next character not null (RESTORE n)

    LAB_161A:
          sec                     // set carry for subtract
          lda   Smeml             // get start of mem low byte
          sbc   #$01              // -1
          ldy   Smemh             // get start of mem high byte
          bcs   LAB_1624          // branch if no underflow

    LAB_uflow:
          dey                     // else decrement high byte
    LAB_1624:
          sta   Dptrl             // save DATA pointer low byte
          sty   Dptrh             // save DATA pointer high byte
    LAB_1628:
          rts

                                  // is RESTORE n
    LAB_RESTOREn:
          jsr   LAB_GFPN          // get fixed-point number into temp integer
          jsr   LAB_SNBL          // scan for next BASIC line
          lda   Clineh            // get current line high byte
          cmp   Itemph            // compare with temporary integer high byte
          bcs   LAB_reset_search  // branch if >= (start search from beginning)

          tya                     // else copy line index to a
          sec                     // set carry (+1)
          adc   Bpntrl            // add BASIC execute pointer low byte
          ldx   Bpntrh            // get BASIC execute pointer high byte
          bcc   LAB_go_search     // branch if no overflow to high byte

          inx                     // increment high byte
          bcs   LAB_go_search     // branch always (can never be carry clear)

    // search for line # in temp (Itempl/Itemph) from start of mem pointer (Smeml)

    LAB_reset_search:
          lda   Smeml             // get start of mem low byte
          ldx   Smemh             // get start of mem high byte

    // search for line # in temp (Itempl/Itemph) from (AX)

    LAB_go_search:

          jsr   LAB_SHLN          // search Basic for temp integer line number from AX
          bcs   LAB_line_found    // if carry set go set pointer

          jmp   LAB_16F7          // else go do "Undefined statement" error

    LAB_line_found:
                                  // carry already set for subtract
          lda   Baslnl            // get pointer low byte
          sbc   #$01              // -1
          ldy   Baslnh            // get pointer high byte
          bcs   LAB_1624          // branch if no underflow (save DATA pointer and return)

          bcc   LAB_uflow         // else decrement high byte then save DATA pointer and
                                  // return (branch always)

    // perform NULL

    LAB_NULL:
          jsr   LAB_GTBY          // get byte parameter
          stx   Nullct            // save new NULL count
    LAB_167A:
          rts

    // perform CONT

    LAB_CONT:
          bne   LAB_167A          // if following byte exit to do syntax error

          ldy   Cpntrh            // get continue pointer high byte
          cpy   #>Ibuffs          // *** fix p2: test direct mode
          bne   LAB_166C          // go do continue if we can

          ldx   #$1E              // error code $1E ("Can't continue" error)
          jmp   LAB_XERR          // do error #x, then warm start

                                  // we can continue so ..
    LAB_166C:
          sty   Bpntrh            // save BASIC execute pointer high byte
          lda   Cpntrl            // get continue pointer low byte
          sta   Bpntrl            // save BASIC execute pointer low byte
          lda   Blinel            // get break line low byte
          ldy   Blineh            // get break line high byte
          sta   Clinel            // set current line low byte
          sty   Clineh            // set current line high byte
          rts

    // perform RUN

    LAB_RUN:
          bne   LAB_1696          // branch if RUN n
          jmp   LAB_1477          // reset execution to start, clear variables, flush stack and
                                  // return

    // does RUN n

    LAB_1696:
          jsr   LAB_147A          // go do "CLEAR"
          beq   LAB_16B0          // get n and do GOTO n (branch always as CLEAR sets Z=1)

    // perform DO

    LAB_DO:
          lda   #$05              // need 5 bytes for DO
          jsr   LAB_1212          // check room on stack for a bytes
          lda   Bpntrh            // get BASIC execute pointer high byte
          pha                     // push on stack
          lda   Bpntrl            // get BASIC execute pointer low byte
          pha                     // push on stack
          lda   Clineh            // get current line high byte
          pha                     // push on stack
          lda   Clinel            // get current line low byte
          pha                     // push on stack
          lda   #TK_DO            // token for DO
          pha                     // push on stack
          jsr   LAB_GBYT          // scan memory
          jmp   LAB_15C2          // go do interpreter inner loop

    // perform GOSUB

    LAB_GOSUB:
          lda   #$05              // need 5 bytes for GOSUB
          jsr   LAB_1212          // check room on stack for a bytes
          lda   Bpntrh            // get BASIC execute pointer high byte
          pha                     // push on stack
          lda   Bpntrl            // get BASIC execute pointer low byte
          pha                     // push on stack
          lda   Clineh            // get current line high byte
          pha                     // push on stack
          lda   Clinel            // get current line low byte
          pha                     // push on stack
          lda   #TK_GOSUB         // token for GOSUB
          pha                     // push on stack
    LAB_16B0:
          jsr   LAB_GBYT          // scan memory
          jsr   LAB_GOTO          // perform GOTO n
          jmp   LAB_15C2          // go do interpreter inner loop
                                  // (can't rts, we used the stack!)

    // perform GOTO

    LAB_GOTO:
          jsr   LAB_GFPN          // get fixed-point number into temp integer
          jsr   LAB_SNBL          // scan for next BASIC line
          lda   Clineh            // get current line high byte
          cmp   Itemph            // compare with temporary integer high byte
          bcs   LAB_16D0          // branch if >= (start search from beginning)

          tya                     // else copy line index to a
          sec                     // set carry (+1)
          adc   Bpntrl            // add BASIC execute pointer low byte
          ldx   Bpntrh            // get BASIC execute pointer high byte
          bcc   LAB_16D4          // branch if no overflow to high byte

          inx                     // increment high byte
          bcs   LAB_16D4          // branch always (can never be carry)

    // search for line # in temp (Itempl/Itemph) from start of mem pointer (Smeml)

    LAB_16D0:
          lda   Smeml             // get start of mem low byte
          ldx   Smemh             // get start of mem high byte

    // search for line # in temp (Itempl/Itemph) from (AX)

    LAB_16D4:
          jsr   LAB_SHLN          // search Basic for temp integer line number from AX
          bcc   LAB_16F7          // if carry clear go do "Undefined statement" error
                                  // (unspecified statement)

                                  // carry already set for subtract
          lda   Baslnl            // get pointer low byte
          sbc   #$01              // -1
          sta   Bpntrl            // save BASIC execute pointer low byte
          lda   Baslnh            // get pointer high byte
          sbc   #$00              // subtract carry
          sta   Bpntrh            // save BASIC execute pointer high byte
    LAB_16E5:
          rts

    LAB_DONOK:
          ldx   #$22              // error code $22 ("LOOP without DO" error)
          jmp   LAB_XERR          // do error #x, then warm start

    // perform LOOP

    LAB_LOOP:
          tay                     // save following token
          tsx                     // copy stack pointer
          lda   LAB_STAK+3,x      // get token byte from stack
          cmp   #TK_DO            // compare with DO token
          bne   LAB_DONOK         // branch if no matching DO

          inx                     // dump calling routine return address
          inx                     // dump calling routine return address
          txs                     // correct stack
          tya                     // get saved following token back
          beq   LoopAlways        // if no following token loop forever
                                  // (stack pointer in x)

          cmp   #':'              // could be ':'
          beq   LoopAlways        // if :... loop forever

          sbc   #TK_UNTIL         // subtract token for UNTIL, we know carry is set here
          tax                     // copy to x (if it was UNTIL then y will be correct)
          beq   DoRest            // branch if was UNTIL

          dex                     // decrement result
          bne   LAB_16FC          // if not WHILE go do syntax error and warm start
                                  // only if the token was WHILE will this fail

          dex                     // set invert result byte
    DoRest:
          stx   Frnxth            // save invert result byte
          jsr   LAB_IGBY          // increment and scan memory
          jsr   LAB_EVEX          // evaluate expression
          lda   FAC1_e            // get FAC1 exponent
          beq   DoCmp             // if =0 go do straight compare

          lda   #$FF              // else set all bits
    DoCmp:
          tsx                     // copy stack pointer
          eor   Frnxth            // eor with invert byte
          bne   LoopDone          // if <> 0 clear stack and back to interpreter loop

                                  // loop condition wasn't met so do it again
    LoopAlways:
          lda   LAB_STAK+2,x      // get current line low byte
          sta   Clinel            // save current line low byte
          lda   LAB_STAK+3,x      // get current line high byte
          sta   Clineh            // save current line high byte
          lda   LAB_STAK+4,x      // get BASIC execute pointer low byte
          sta   Bpntrl            // save BASIC execute pointer low byte
          lda   LAB_STAK+5,x      // get BASIC execute pointer high byte
          sta   Bpntrh            // save BASIC execute pointer high byte
          jsr   LAB_GBYT          // scan memory
          jmp   LAB_15C2          // go do interpreter inner loop

                                  // clear stack and back to interpreter loop
    LoopDone:
          inx                     // dump DO token
          inx                     // dump current line low byte
          inx                     // dump current line high byte
          inx                     // dump BASIC execute pointer low byte
          inx                     // dump BASIC execute pointer high byte
          txs                     // correct stack
          jmp   LAB_DATA          // go perform DATA (find : or [EOL])

    // do the return without gosub error
    LAB_16F4:
          ldx   #$04              // error code $04 ("RETURN without GOSUB" error)
          define byte = $2C       // makes next line bit LAB_0EA2

    LAB_16F7:                     // do undefined statement error:
          ldx   #$0E              // error code $0E ("Undefined statement" error)
          jmp   LAB_XERR          // do error #x, then warm start

    // perform RETURN
    LAB_RETURN:
          bne   LAB_16E5          // exit if following token (to allow syntax error)

    LAB_16E8:
          pla                     // dump calling routine return address
          pla                     // dump calling routine return address
          pla                     // pull token
          cmp   #TK_GOSUB         // compare with GOSUB token
          bne   LAB_16F4          // branch if no matching GOSUB

    LAB_16FF:
          pla                     // pull current line low byte
          sta   Clinel            // save current line low byte
          pla                     // pull current line high byte
          sta   Clineh            // save current line high byte
          pla                     // pull BASIC execute pointer low byte
          sta   Bpntrl            // save BASIC execute pointer low byte
          pla                     // pull BASIC execute pointer high byte
          sta   Bpntrh            // save BASIC execute pointer high byte

                                  // now do the DATA statement as we could be returning into
                                  // the middle of an ON <var> GOSUB n,m,p,q line
                                  // (the return address used by the DATA statement is the one
                                  // pushed before the GOSUB was executed!)

    // perform DATA
    LAB_DATA:
          jsr   LAB_SNBS          // scan for next BASIC statement ([:] or [EOL])

                                  // set BASIC execute pointer
    LAB_170F:
          tya                     // copy index to a
          clc                     // clear carry for add
          adc   Bpntrl            // add BASIC execute pointer low byte
          sta   Bpntrl            // save BASIC execute pointer low byte
          bcc   LAB_1719          // skip next if no carry

          inc   Bpntrh            // else increment BASIC execute pointer high byte
    LAB_1719:
          rts

    LAB_16FC:
          jmp   LAB_SNER          // do syntax error then warm start

    // scan for next BASIC statement ([:] or [EOL])
    // returns y as index to [:] or [EOL]

    LAB_SNBS:
          ldx   #':'              // set look for character = ":"
          define byte = $2C       // makes next line bit $00A2

    // scan for next BASIC line
    // returns y as index to [EOL]

    LAB_SNBL:
          ldx   #$00              // set alt search character = [EOL]
          ldy   #$00              // set search character = [EOL]
          sty   Asrch             // store search character
    LAB_1725:
          txa                     // get alt search character
          eor   Asrch             // toggle search character, effectively swap with $00
          sta   Asrch             // save swapped search character
    LAB_172D:
          lda   (Bpntrl),y        // get next byte
          beq   LAB_1719          // exit if null [EOL]

          cmp   Asrch             // compare with search character
          beq   LAB_1719          // exit if found

          iny                     // increment index
          cmp   #$22              // compare current character with open quote
          bne   LAB_172D          // if not open quote go get next character

          beq   LAB_1725          // if found go swap search character for alt search character

    // perform IF

    LAB_IF:
          jsr   LAB_EVEX          // evaluate the expression
          jsr   LAB_GBYT          // scan memory
          cmp   #TK_THEN          // compare with THEN token
          beq   LAB_174B          // if it was THEN go do IF

                                  // wasn't IF .. THEN so must be IF .. GOTO
          cmp   #TK_GOTO          // compare with GOTO token
          bne   LAB_16FC          // if it wasn't GOTO go do syntax error

          ldx   Bpntrl            // save the basic pointer low byte
          ldy   Bpntrh            // save the basic pointer high byte
          jsr   LAB_IGBY          // increment and scan memory
          bcs   LAB_16FC          // if not numeric go do syntax error

          stx   Bpntrl            // restore the basic pointer low byte
          sty   Bpntrh            // restore the basic pointer high byte
    LAB_174B:
          lda   FAC1_e            // get FAC1 exponent
          beq   LAB_174E          // if the result was zero go look for an ELSE

          jsr   LAB_IGBY          // else increment and scan memory
          bcs   LAB_174D          // if not numeric go do var or keyword

    LAB_174C:
          jmp   LAB_GOTO          // else was numeric so do GOTO n

                                  // is var or keyword
    LAB_174D:
    // *** patch       allow NEXT, LOOP & RETURN to find FOR, DO or GOSUB structure on stack
    // *** replace
    //      cmp   #TK_RETURN        // compare the byte with the token for RETURN
    //      bne   LAB_174G          // if it wasn't RETURN go interpret BASIC code from (Bpntrl)
    //                              // and return to this code to process any following code
    //
    //      jmp   LAB_1602          // else it was RETURN so interpret BASIC code from (Bpntrl)
    //                              // but don't return here
    //
    //LAB_174G
    //      jsr   LAB_15FF          // interpret BASIC code from (Bpntrl)
    //
    //// the IF was executed and there may be a following ELSE so the code needs to return
    //// here to check and ignore the ELSE if present
    //
    //      ldy   #$00              // clear the index
    //      lda   (Bpntrl),y        // get the next BASIC byte
    //      cmp   #TK_ELSE          // compare it with the token for ELSE
    //      beq   LAB_DATA          // if ELSE ignore the following statement
    //
    //// there was no ELSE so continue execution of IF <expr> THEN <stat> [: <stat>]. any
    //// following ELSE will, correctly, cause a syntax error
    //
    //      rts                     // else return to the interpreter inner loop
    //
    // *** with
          pla                     // discard interpreter loop return address
          pla                     // so data structures are at the correct stack offset
          jsr   LAB_GBYT          // restore token or variable
          jsr   LAB_15FF          // interpret BASIC code from (Bpntrl)

    // the IF was executed and there may be a following ELSE so the code needs to return
    // here to check and ignore the ELSE if present

          ldy   #$00              // clear the index
          lda   (Bpntrl),y        // get the next BASIC byte
          cmp   #TK_ELSE          // compare it with the token for ELSE
          bne   LAB_no_ELSE       // no - continue on this line
          jsr   LAB_DATA          // yes - skip the rest of the line

    // there was no ELSE so continue execution of IF <expr> THEN <stat> [: <stat>]. any
    // following ELSE will, correctly, cause a syntax error

    LAB_no_ELSE:
          jmp LAB_15C2            // return to the interpreter inner loop
    // *** end patch  allow NEXT, LOOP & RETURN to find FOR, DO or GOSUB structure on stack

    // perform ELSE after IF

    LAB_174E:
          ldy   #$00              // clear the BASIC byte index
          ldx   #$01              // clear the nesting depth
    LAB_1750:
          iny                     // increment the BASIC byte index
          lda   (Bpntrl),y        // get the next BASIC byte
          beq   LAB_1753          // if EOL go add the pointer and return

          cmp   #TK_IF            // compare the byte with the token for IF
          bne   LAB_1752          // if not IF token skip the depth increment

          inx                     // else increment the nesting depth ..
          bne   LAB_1750          // .. and continue looking

    LAB_1752:
          cmp   #TK_ELSE          // compare the byte with the token for ELSE
          bne   LAB_1750          // if not ELSE token continue looking

          dex                     // was ELSE so decrement the nesting depth
          bne   LAB_1750          // loop if still nested

          iny                     // increment the BASIC byte index past the ELSE

    // found the matching ELSE, now do <{n|statement}>

    LAB_1753:
          tya                     // else copy line index to a
          clc                     // clear carry for add
          adc   Bpntrl            // add the BASIC execute pointer low byte
          sta   Bpntrl            // save the BASIC execute pointer low byte
          bcc   LAB_1754          // branch if no overflow to high byte

          inc   Bpntrh            // else increment the BASIC execute pointer high byte
    LAB_1754:
          jsr   LAB_GBYT          // scan memory
          bcc   LAB_174C          // if numeric do GOTO n
                                  // the code will return to the interpreter loop at the
                                  // tail end of the GOTO <n>

          jmp   LAB_15FF          // interpret BASIC code from (Bpntrl)
                                  // the code will return to the interpreter loop at the
                                  // tail end of the <statement>

    // perform REM, skip (rest of) line

    LAB_REM:
          jsr   LAB_SNBL          // scan for next BASIC line
          jmp   LAB_170F          // go set BASIC execute pointer and return, branch always

    LAB_16FD:
          jmp   LAB_SNER          // do syntax error then warm start

    // perform ON

    LAB_ON:
    LAB_NONM:
          jsr   LAB_GTBY          // get byte parameter
          pha                     // push GOTO/GOSUB token
          cmp   #TK_GOSUB         // compare with GOSUB token
          beq   LAB_176B          // branch if GOSUB

          cmp   #TK_GOTO          // compare with GOTO token
    LAB_1767:
          bne   LAB_16FD          // if not GOTO do syntax error then warm start


    // next character was GOTO or GOSUB

    LAB_176B:
          dec   FAC1_3            // decrement index (byte value)
          bne   LAB_1773          // branch if not zero

          pla                     // pull GOTO/GOSUB token
          jmp   LAB_1602          // go execute it

    LAB_1773:
          jsr   LAB_IGBY          // increment and scan memory
          jsr   LAB_GFPN          // get fixed-point number into temp integer (skip this n)
                                  // (we could ldx #',' and jsr LAB_SNBL+2, then we
                                  // just bne LAB_176B for the loop. should be quicker ..
                                  // no we can't, what if we meet a colon or [EOL]?)
          cmp   #$2C              // compare next character with ","
          beq   LAB_176B          // loop if ","

    LAB_177E:
          pla                     // else pull keyword token (run out of options)
                                  // also dump +/-1 pointer low byte and exit
    LAB_177F:
          rts

    // takes n * 106 + 11 cycles where n is the number of digits

    // get fixed-point number into temp integer

    LAB_GFPN:
          ldx   #$00              // clear reg
          stx   Itempl            // clear temporary integer low byte
    LAB_1785:
          stx   Itemph            // save temporary integer high byte
          bcs   LAB_177F          // return if carry set, end of scan, character was
                                  // not 0-9

          cpx   #$19              // compare high byte with $19
          tay                     // ensure Zb = 0 if the branch is taken
          bcs   LAB_1767          // branch if >=, makes max line # 63999 because next
                                  // bit does *$0A, = 64000, compare at target will fail
                                  // and do syntax error

          sbc   #'0'-1            // subtract "0", $2F + carry, from byte
          tay                     // copy binary digit
          lda   Itempl            // get temporary integer low byte
          asl                     // *2 low byte
          rol   Itemph            // *2 high byte
          asl                     // *2 low byte
          rol   Itemph            // *2 high byte, *4
          adc   Itempl            // + low byte, *5
          sta   Itempl            // save it
          txa                     // get high byte copy to a
          adc   Itemph            // + high byte, *5
          asl   Itempl            // *2 low byte, *10d
          rol                     // *2 high byte, *10d
          tax                     // copy high byte back to x
          tya                     // get binary digit back
          adc   Itempl            // add number low byte
          sta   Itempl            // save number low byte
          bcc   LAB_17B3          // if no overflow to high byte get next character

          inx                     // else increment high byte
    LAB_17B3:
          jsr   LAB_IGBY          // increment and scan memory
          jmp   LAB_1785          // loop for next character

    // perform dec

    LAB_DEC:
          lda   #<LAB_2AFD        // set -1 pointer low byte
          define byte = $2C       // bit abs to skip the lda below

    // perform inc

    LAB_INC:
          lda   #<LAB_259C        // set 1 pointer low byte
    LAB_17B5:
          pha                     // save +/-1 pointer low byte
    LAB_17B7:
          jsr   LAB_GVAR          // get var address
          ldx   Dtypef            // get data type flag, $FF=string, $00=numeric
          bmi   IncrErr           // exit if string

          sta   Lvarpl            // save var address low byte
          sty   Lvarph            // save var address high byte
          jsr   LAB_UFAC          // unpack memory (AY) into FAC1
          pla                     // get +/-1 pointer low byte
          pha                     // save +/-1 pointer low byte
          ldy   #>LAB_259C        // set +/-1 pointer high byte (both the same)
          jsr   LAB_246C          // add (AY) to FAC1
          jsr   LAB_PFAC          // pack FAC1 into variable (Lvarpl)

          jsr   LAB_GBYT          // scan memory
          cmp   #','              // compare with ","
          bne   LAB_177E          // exit if not "," (either end or error)

                                  // was "," so another INCR variable to do
          jsr   LAB_IGBY          // increment and scan memory
          jmp   LAB_17B7          // go do next var

    IncrErr:
          jmp   LAB_1ABC          // do "Type mismatch" error then warm start

    // perform LET
    LAB_LET:
          jsr   LAB_GVAR          // get var address
          sta   Lvarpl            // save var address low byte
          sty   Lvarph            // save var address high byte
          lda   #TK_EQUAL         // get = token
          jsr   LAB_SCCA          // scan for CHR$(a), else do syntax error then warm start
          lda   Dtypef            // get data type flag, $FF=string, $00=numeric
          pha                     // push data type flag
          jsr   LAB_EVEX          // evaluate expression
          pla                     // pop data type flag
          rol                     // set carry if type = string
    // *** begin patch  result of a string compare stores string pointer to variable
    //                  but should store FAC1 (true/false value)
    // *** replace
    //      jsr   LAB_CKTM          // type match check, set C for string
    //      bne   LAB_17D5          // branch if string
    // *** with
          jsr   LAB_CKTM          // type match check, keep C (expected type)
          bcs   LAB_17D5          // branch if string
    // *** end patch

          jmp   LAB_PFAC          // pack FAC1 into variable (Lvarpl) and return

    // string LET

    LAB_17D5:
          ldy   #$02              // set index to pointer high byte
          lda   (des_pl),y        // get string pointer high byte
          cmp   Sstorh            // compare bottom of string space high byte
          bcc   LAB_17F4          // if less assign value and exit (was in program memory)

          bne   LAB_17E6          // branch if >
                                  // else was equal so compare low bytes
          dey                     // decrement index
          lda   (des_pl),y        // get pointer low byte
          cmp   Sstorl            // compare bottom of string space low byte
          bcc   LAB_17F4          // if less assign value and exit (was in program memory)

                                  // pointer was >= to bottom of string space pointer
    LAB_17E6:
          ldy   des_ph            // get descriptor pointer high byte
          cpy   Svarh             // compare start of vars high byte
          bcc   LAB_17F4          // branch if less (descriptor is on stack)

          bne   LAB_17FB          // branch if greater (descriptor is not on stack)

                                  // else high bytes were equal so ..
          lda   des_pl            // get descriptor pointer low byte
          cmp   Svarl             // compare start of vars low byte
          bcs   LAB_17FB          // branch if >= (descriptor is not on stack)

    LAB_17F4:
          lda   des_pl            // get descriptor pointer low byte
          ldy   des_ph            // get descriptor pointer high byte
          jmp   LAB_1811          // clean stack, copy descriptor to variable and return

                                  // make space and copy string
    LAB_17FB:
          ldy   #$00              // index to length
          lda   (des_pl),y        // get string length
          jsr   LAB_209C          // copy string
          lda   des_2l            // get descriptor pointer low byte
          ldy   des_2h            // get descriptor pointer high byte
          sta   ssptr_l           // save descriptor pointer low byte
          sty   ssptr_h           // save descriptor pointer high byte
          jsr   LAB_228A          // copy string from descriptor (sdescr) to (Sutill)
          lda   #<FAC1_e          // set descriptor pointer low byte
          ldy   #>FAC1_e          // get descriptor pointer high byte

                                  // clean stack and assign value to string variable
    LAB_1811:
          sta   des_2l            // save descriptor_2 pointer low byte
          sty   des_2h            // save descriptor_2 pointer high byte
          jsr   LAB_22EB          // clean descriptor stack, YA = pointer
          ldy   #$00              // index to length
          lda   (des_2l),y        // get string length
          sta   (Lvarpl),y        // copy to let string variable
          iny                     // index to string pointer low byte
          lda   (des_2l),y        // get string pointer low byte
          sta   (Lvarpl),y        // copy to let string variable
          iny                     // index to string pointer high byte
          lda   (des_2l),y        // get string pointer high byte
          sta   (Lvarpl),y        // copy to let string variable
          rts

    // perform GET

    LAB_GET:
          jsr   LAB_GVAR          // get var address
          sta   Lvarpl            // save var address low byte
          sty   Lvarph            // save var address high byte
          jsr   INGET             // get input byte
          ldx   Dtypef            // get data type flag, $FF=string, $00=numeric
          bmi   LAB_GETS          // go get string character

                                  // was numeric get
          tay                     // copy character to y
          jsr   LAB_1FD0          // convert y to byte in FAC1
          jmp   LAB_PFAC          // pack FAC1 into variable (Lvarpl) and return

    LAB_GETS:
          pha                     // save character
          lda   #$01              // string is single byte
          bcs   LAB_IsByte        // branch if byte received

          pla                     // string is null
    LAB_IsByte:
          jsr   LAB_MSSP          // make string space a bytes long a=$AC=length,
                                  // x=$AD=Sutill=ptr low byte, y=$AE=Sutilh=ptr high byte
          beq   LAB_NoSt          // skip store if null string

          pla                     // get character back
          ldy   #$00              // clear index
          sta   (str_pl),y        // save byte in string (byte IS string!)
    LAB_NoSt:
          jsr   LAB_RTST          // check for space on descriptor stack then put address
                                  // and length on descriptor stack and update stack pointers

          jmp   LAB_17D5          // do string LET and return

    // perform PRINT

    LAB_1829:
          jsr   LAB_18C6          // print string from Sutill/Sutilh
    LAB_182C:
          jsr   LAB_GBYT          // scan memory

    // PRINT

    LAB_PRINT:
          beq   LAB_CRLF          // if nothing following just print CR/LF

    LAB_1831:
          cmp   #TK_TAB           // compare with TAB( token
          beq   LAB_18A2          // go do TAB/SPC

          cmp   #TK_SPC           // compare with SPC( token
          beq   LAB_18A2          // go do TAB/SPC

          cmp   #','              // compare with ","
          beq   LAB_188B          // go do move to next TAB mark

          cmp   #';'              // compare with ";"
          beq   LAB_18BD          // if ";" continue with PRINT processing

          jsr   LAB_EVEX          // evaluate expression
          bit   Dtypef            // test data type flag, $FF=string, $00=numeric
          bmi   LAB_1829          // branch if string

          jsr   LAB_296E          // convert FAC1 to string
          jsr   LAB_20AE          // print " terminated string to Sutill/Sutilh
          ldy   #$00              // clear index

    // don't check fit if terminal width byte is zero

          lda   TWidth            // get terminal width byte
          beq   LAB_185E          // skip check if zero

          sec                     // set carry for subtract
          sbc   TPos              // subtract terminal position
          sbc   (des_pl),y        // subtract string length
          bcs   LAB_185E          // branch if less than terminal width

          jsr   LAB_CRLF          // else print CR/LF
    LAB_185E:
          jsr   LAB_18C6          // print string from Sutill/Sutilh
          beq   LAB_182C          // always go continue processing line

    // CR/LF return to BASIC from BASIC input handler

    LAB_1866:
          lda   #$00              // clear byte
          sta   Ibuffs,x          // null terminate input
          ldx   #<Ibuffs          // set x to buffer start-1 low byte
          ldy   #>Ibuffs          // set y to buffer start-1 high byte

    // print CR/LF

    LAB_CRLF:
          lda   #CR               // load [CR]
          jsr   LAB_PRNA          // go print the character
          lda   #LF               // load [LF]
          bne   LAB_PRNA          // go print the character and return, branch always

    LAB_188B:
          lda   TPos              // get terminal position
          cmp   Iclim             // compare with input column limit
          bcc   LAB_1897          // branch if less

          jsr   LAB_CRLF          // else print CR/LF (next line)
          bne   LAB_18BD          // continue with PRINT processing (branch always)

    LAB_1897:
          sec                     // set carry for subtract
    LAB_1898:
          sbc   TabSiz            // subtract TAB size
          bcs   LAB_1898          // loop if result was +ve

          eor   #$FF              // complement it
          adc   #$01              // +1 (twos complement)
          bne   LAB_18B6          // always print a spaces (result is never $00)

                                  // do TAB/SPC
    LAB_18A2:
          pha                     // save token
          jsr   LAB_SGBY          // scan and get byte parameter
          cmp   #$29              // is next character )
          bne   LAB_1910          // if not do syntax error then warm start

          pla                     // get token back
          cmp   #TK_TAB           // was it TAB ?
          bne   LAB_18B7          // if not go do SPC

                                  // calculate TAB offset
          txa                     // copy integer value to a
          sbc   TPos              // subtract terminal position
          bcc   LAB_18BD          // branch if result was < 0 (can't TAB backwards)

                                  // print a spaces
    LAB_18B6:
          tax                     // copy result to x
    LAB_18B7:
          txa                     // set flags on size for SPC
          beq   LAB_18BD          // branch if result was = $0, already here

                                  // print x spaces
    LAB_18BA:
          jsr   LAB_18E0          // print " "
          dex                     // decrement count
          bne   LAB_18BA          // loop if not all done

                                  // continue with PRINT processing
    LAB_18BD:
          jsr   LAB_IGBY          // increment and scan memory
          bne   LAB_1831          // if more to print go do it

          rts

    // print null terminated string from memory

    LAB_18C3:
          jsr   LAB_20AE          // print 0-terminated string to Sutill/Sutilh

    // print string from Sutill/Sutilh

    LAB_18C6:
          jsr   LAB_22B6          // pop string off descriptor stack, or from top of string
                                  // space returns with a = length, x=$71=pointer low byte,
                                  // y=$72=pointer high byte
          ldy   #$00              // reset index
          tax                     // copy length to x
          beq   LAB_188C          // exit (rts) if null string

    LAB_18CD:

          lda   (ut1_pl),y        // get next byte
          jsr   LAB_PRNA          // go print the character
          iny                     // increment index
          dex                     // decrement count
          bne   LAB_18CD          // loop if not done yet

          rts

                                  // Print single format character
    // print " "

    LAB_18E0:
          lda   #$20              // load " "
          define byte = $2C       // change next line to bit LAB_3FA9

    // print "?" character

    LAB_18E3:
          lda   #$3F              // load "?" character

    // print character in a
    // now includes the null handler
    // also includes infinite line length code
    // note! some routines expect this one to exit with Zb=0

    LAB_PRNA:
          cmp   #' '              // compare with " "
          bcc   LAB_18F9          // branch if less (non printing)

                                  // else printable character
          pha                     // save the character

    // don't check fit if terminal width byte is zero

          lda   TWidth            // get terminal width
          bne   LAB_18F0          // branch if not zero (not infinite length)

    // is "infinite line" so check TAB position

          lda   TPos              // get position
          sbc   TabSiz            // subtract TAB size, carry set by cmp #$20 above
          bne   LAB_18F7          // skip reset if different

          sta   TPos              // else reset position
          beq   LAB_18F7          // go print character

    LAB_18F0:
          cmp   TPos              // compare with terminal character position
          bne   LAB_18F7          // branch if not at end of line

          jsr   LAB_CRLF          // else print CR/LF
    LAB_18F7:
          inc   TPos              // increment terminal position
          pla                     // get character back
    LAB_18F9:
          jsr   V_OUTP            // output byte via output vector
          cmp   #$0D              // compare with [CR]
          bne   LAB_188A          // branch if not [CR]

                                  // else print nullct nulls after the [CR]
          stx   TempB             // save buffer index
          ldx   Nullct            // get null count
          beq   LAB_1886          // branch if no nulls

          lda   #$00              // load [NULL]
    LAB_1880:
          jsr   LAB_PRNA          // go print the character
          dex                     // decrement count
          bne   LAB_1880          // loop if not all done

          lda   #$0D              // restore the character (and set the flags)
    LAB_1886:
          stx   TPos              // clear terminal position (x always = zero when we get here)
          ldx   TempB             // restore buffer index
    LAB_188A:
          and   #$FF              // set the flags
    LAB_188C:
          rts

    // handle bad input data

    LAB_1904:
          lda   Imode             // get input mode flag, $00=INPUT, $00=READ
          bpl   LAB_1913          // branch if INPUT (go do redo)

          lda   Dlinel            // get current DATA line low byte
          ldy   Dlineh            // get current DATA line high byte
          sta   Clinel            // save current line low byte
          sty   Clineh            // save current line high byte
    LAB_1910:
          jmp   LAB_SNER          // do syntax error then warm start

                                  // mode was INPUT
    LAB_1913:
          lda   #<LAB_REDO        // point to redo message (low addr)
          ldy   #>LAB_REDO        // point to redo message (high addr)
          jsr   LAB_18C3          // print null terminated string from memory
          lda   Cpntrl            // get continue pointer low byte
          ldy   Cpntrh            // get continue pointer high byte
          sta   Bpntrl            // save BASIC execute pointer low byte
          sty   Bpntrh            // save BASIC execute pointer high byte
          rts

    // perform INPUT

    LAB_INPUT:
          cmp   #$22              // compare next byte with open quote
          bne   LAB_1934          // branch if no prompt string

          jsr   LAB_1BC1          // print "..." string
          lda   #$3B              // load a with ";"
          jsr   LAB_SCCA          // scan for CHR$(a), else do syntax error then warm start
          jsr   LAB_18C6          // print string from Sutill/Sutilh

                                  // done with prompt, now get data
    LAB_1934:
          jsr   LAB_CKRN          // check not Direct, back here if ok
          jsr   LAB_INLN          // print "? " and get BASIC input
          lda   #$00              // set mode = INPUT
          cmp   Ibuffs            // test first byte in buffer
          bne   LAB_1953          // branch if not null input

    // *** change p2: keep carry set to throw break message
    //      clc                     // was null input so clear carry to exit program
          jmp   LAB_1647          // go do BREAK exit

    // perform READ

    LAB_READ:
          ldx   Dptrl             // get DATA pointer low byte
          ldy   Dptrh             // get DATA pointer high byte
          lda   #$80              // set mode = READ

    LAB_1953:
          sta   Imode             // set input mode flag, $00=INPUT, $80=READ
          stx   Rdptrl            // save READ pointer low byte
          sty   Rdptrh            // save READ pointer high byte

                                  // READ or INPUT next variable from list
    LAB_195B:
          jsr   LAB_GVAR          // get (var) address
          sta   Lvarpl            // save address low byte
          sty   Lvarph            // save address high byte
          lda   Bpntrl            // get BASIC execute pointer low byte
          ldy   Bpntrh            // get BASIC execute pointer high byte
          sta   Itempl            // save as temporary integer low byte
          sty   Itemph            // save as temporary integer high byte
          ldx   Rdptrl            // get READ pointer low byte
          ldy   Rdptrh            // get READ pointer high byte
          stx   Bpntrl            // set BASIC execute pointer low byte
          sty   Bpntrh            // set BASIC execute pointer high byte
          jsr   LAB_GBYT          // scan memory
          bne   LAB_1988          // branch if not null

                                  // pointer was to null entry
          bit   Imode             // test input mode flag, $00=INPUT, $80=READ
          bmi   LAB_19DD          // branch if READ

                                  // mode was INPUT
          jsr   LAB_18E3          // print "?" character (double ? for extended input)
          jsr   LAB_INLN          // print "? " and get BASIC input
          stx   Bpntrl            // set BASIC execute pointer low byte
          sty   Bpntrh            // set BASIC execute pointer high byte
    LAB_1985:
          jsr   LAB_GBYT          // scan memory
    LAB_1988:
          bit   Dtypef            // test data type flag, $FF=string, $00=numeric
          bpl   LAB_19B0          // branch if numeric

                                  // else get string
          sta   Srchc             // save search character
          cmp   #$22              // was it " ?
          beq   LAB_1999          // branch if so

          lda   #':'              // else search character is ":"
          sta   Srchc             // set new search character
          lda   #','              // other search character is ","
          clc                     // clear carry for add
    LAB_1999:
          sta   Asrch             // set second search character
          lda   Bpntrl            // get BASIC execute pointer low byte
          ldy   Bpntrh            // get BASIC execute pointer high byte

          adc   #$00              // c is =1 if we came via the beq LAB_1999, else =0
          bcc   LAB_19A4          // branch if no execute pointer low byte rollover

          iny                     // else increment high byte
    LAB_19A4:
          jsr   LAB_20B4          // print Srchc or Asrch terminated string to Sutill/Sutilh
          jsr   LAB_23F3          // restore BASIC execute pointer from temp (Btmpl/Btmph)
          jsr   LAB_17D5          // go do string LET
          jmp   LAB_19B6          // go check string terminator

                                  // get numeric INPUT
    LAB_19B0:
          jsr   LAB_2887          // get FAC1 from string
          jsr   LAB_PFAC          // pack FAC1 into (Lvarpl)
    LAB_19B6:
          jsr   LAB_GBYT          // scan memory
          beq   LAB_19C5          // branch if null (last entry)

          cmp   #','              // else compare with ","
          beq   LAB_19C2          // branch if ","

          jmp   LAB_1904          // else go handle bad input data

                                  // got good input data
    LAB_19C2:
          jsr   LAB_IGBY          // increment and scan memory
    LAB_19C5:
          lda   Bpntrl            // get BASIC execute pointer low byte (temp READ/INPUT ptr)
          ldy   Bpntrh            // get BASIC execute pointer high byte (temp READ/INPUT ptr)
          sta   Rdptrl            // save for now
          sty   Rdptrh            // save for now
          lda   Itempl            // get temporary integer low byte (temp BASIC execute ptr)
          ldy   Itemph            // get temporary integer high byte (temp BASIC execute ptr)
          sta   Bpntrl            // set BASIC execute pointer low byte
          sty   Bpntrh            // set BASIC execute pointer high byte
          jsr   LAB_GBYT          // scan memory
          beq   LAB_1A03          // if null go do extra ignored message

          jsr   LAB_1C01          // else scan for "," , else do syntax error then warm start
          jmp   LAB_195B          // go INPUT next variable from list

                                  // find next DATA statement or do "Out of DATA" error
    LAB_19DD:
          jsr   LAB_SNBS          // scan for next BASIC statement ([:] or [EOL])
          iny                     // increment index
          tax                     // copy character ([:] or [EOL])
          bne   LAB_19F6          // branch if [:]

          ldx   #$06              // set for "Out of DATA" error
          iny                     // increment index, now points to next line pointer high byte
          lda   (Bpntrl),y        // get next line pointer high byte
          beq   LAB_1A54          // branch if end (eventually does error x)

          iny                     // increment index
          lda   (Bpntrl),y        // get next line # low byte
          sta   Dlinel            // save current DATA line low byte
          iny                     // increment index
          lda   (Bpntrl),y        // get next line # high byte
          iny                     // increment index
          sta   Dlineh            // save current DATA line high byte
    LAB_19F6:
          lda   (Bpntrl),y        // get byte
          iny                     // increment index
          tax                     // copy to x
          jsr   LAB_170F          // set BASIC execute pointer
          cpx   #TK_DATA          // compare with "DATA" token
          beq   LAB_1985          // was "DATA" so go do next READ

          bne   LAB_19DD          // go find next statement if not "DATA"

    // end of INPUT/READ routine

    LAB_1A03:
          lda   Rdptrl            // get temp READ pointer low byte
          ldy   Rdptrh            // get temp READ pointer high byte
          ldx   Imode             // get input mode flag, $00=INPUT, $80=READ
          bpl   LAB_1A0E          // branch if INPUT

          jmp   LAB_1624          // save AY as DATA pointer and return

                                  // we were getting INPUT
    LAB_1A0E:
          ldy   #$00              // clear index
          lda   (Rdptrl),y        // get next byte
          bne   LAB_1A1B          // error if not end of INPUT

          rts

                                  // user typed too much
    LAB_1A1B:
          lda   #<LAB_IMSG        // point to extra ignored message (low addr)
          ldy   #>LAB_IMSG        // point to extra ignored message (high addr)
          jmp   LAB_18C3          // print null terminated string from memory and return

    // search the stack for FOR activity
    // exit with z=1 if FOR else exit with z=0

    LAB_11A1:
          tsx                     // copy stack pointer
          inx                     // +1 pass return address
          inx                     // +2 pass return address
          inx                     // +3 pass calling routine return address
          inx                     // +4 pass calling routine return address
    LAB_11A6:
          lda   LAB_STAK+1,x      // get token byte from stack
          cmp   #TK_FOR           // is it FOR token
          bne   LAB_11CE          // exit if not FOR token

                                  // was FOR token
          lda   Frnxth            // get var pointer for FOR/NEXT high byte
          bne   LAB_11BB          // branch if not null
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
