NollKollTroll/PZ1_Pico/pico_sw/fileSystem.h

/*
Written in 2022 by Adam Klotblixt (adam.klotblixt@gmail.com)

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
You should have received a copy of the CC0 Public Domain Dedication
along with this software. If not, see
<http://creativecommons.org/publicdomain/zero/1.0/>.
*/

#ifndef FILESYSTEM_H
#define FILESYSTEM_H

enum class FILE_CMD 
{
    OPEN_R,
    OPEN_W,
    CLOSE,
    READ,
    WRITE,
    DIR,
    DIR_NEXT
};
enum class FILE_STATE 
{
    OPEN_R,
    OPEN_W,
    OPENED_R,
    OPENED_W,
    CLOSED,
    DIR
};
enum class FILE_STATUS 
{
    OK,
    NOK
};

File fileData, root;
String dirData;
uint8_t dirDataPtr = 0;

char fileName[256];
uint8_t fileNameIndex;
FILE_STATUS fileStatus;
FILE_STATE fileState;

void fsInit()
{
    SPI.setRX(SPI_RX);
    SPI.setTX(SPI_TX);
    SPI.setSCK(SPI_CLK);
    SPI.setCS(SD_CS_N);
    digitalWrite(SD_CS_N, LOW);    
    if (!SD.begin(SD_CS_N)) 
    {
        SerDebug.println("\n*** FS open NOK!");
    }
    else
    {
        SerDebug.println("\n*** FS open OK");
    }
    fileStatus = FILE_STATUS::NOK;
    fileState = FILE_STATE::CLOSED;
    fileNameIndex = 0;
}

static inline void fsCmdWrite(uint8_t cpuData)    
{
    if ((FILE_CMD)cpuData == FILE_CMD::OPEN_R)
    {
        fileStatus = FILE_STATUS::OK;
        fileState = FILE_STATE::OPEN_R;
        fileNameIndex = 0;
    }
    else if ((FILE_CMD)cpuData == FILE_CMD::OPEN_W) 
    {
        fileStatus = FILE_STATUS::OK;
        fileState = FILE_STATE::OPEN_W;
        fileNameIndex = 0;
    }
    else if ((FILE_CMD)cpuData == FILE_CMD::CLOSE) 
    {
        fileData.close();
        fileStatus = FILE_STATUS::OK;
        fileState = FILE_STATE::CLOSED;
    }
    else if ((FILE_CMD)cpuData == FILE_CMD::DIR) 
    {        
        root = SD.open("/");
        if (root) 
        {
            fileStatus = FILE_STATUS::OK;
            fileState = FILE_STATE::DIR;
        }
        else 
        {
            root.close();
            fileStatus = FILE_STATUS::NOK;
            fileState = FILE_STATE::CLOSED;
        }       
    }
    else if ((FILE_CMD)cpuData == FILE_CMD::DIR_NEXT) 
    {
        fileData = root.openNextFile();
        if (fileData) 
        {
            if (!fileData.isDirectory()) 
            {
                dirData = fileData.name() + String(" @") + String((long unsigned int)fileData.size());
            }
            else 
            {
                dirData = String('[') + fileData.name() + String(']');
            }
            dirDataPtr = 0;
        }
        else 
        {
            root.close();
            fileStatus = FILE_STATUS::NOK;
            fileState = FILE_STATE::CLOSED;
        }
    }
}

static inline uint8_t fsDataRead()
{
    uint8_t cpuData;
    if (fileState == FILE_STATE::OPENED_R) 
    {
        if (fileData.available()) 
        {
            fileStatus = FILE_STATUS::OK;
            cpuData = fileData.read();
        }
        else 
        {
            fileStatus = FILE_STATUS::NOK;     
            cpuData = 0;
        }
    }       
    else if (fileState == FILE_STATE::DIR) 
    {
        char retChar = dirData[dirDataPtr];
        if (retChar != 0) 
        {
            dirDataPtr++;
        }
        cpuData = retChar;
    }
    else 
    {
        fileStatus = FILE_STATUS::NOK;
        cpuData = 0;
    }
    return cpuData;
}

static inline void fsDataWrite(uint8_t cpuData)
{
    if(fileState == FILE_STATE::OPENED_W) 
    {
        fileData.write(cpuData);
    }
    else if ((fileState == FILE_STATE::OPEN_R) || 
             (fileState == FILE_STATE::OPEN_W)) 
    {
        if (cpuData == 0) { // if end of string 0-termination
            fileName[fileNameIndex] = 0;
            if (fileState == FILE_STATE::OPEN_W) 
            {
                fileData = SD.open(fileName, FILE_WRITE);
                if (fileData) 
                {
                    fileStatus = FILE_STATUS::OK;
                    fileState = FILE_STATE::OPENED_W;
                }
                else 
                {
                    fileData.close();
                    fileStatus = FILE_STATUS::NOK;
                    fileState = FILE_STATE::CLOSED;
                }
            }                            
            else if (fileState == FILE_STATE::OPEN_R) 
            {
                fileData = SD.open(fileName, FILE_READ);
                if (fileData) 
                {
                    fileStatus = FILE_STATUS::OK;
                    fileState = FILE_STATE::OPENED_R;
                }
                else 
                {
                    fileData.close();
                    fileStatus = FILE_STATUS::NOK;
                    fileState = FILE_STATE::CLOSED;
                }
            }                            
        }
        else if (fileNameIndex < (sizeof(fileName) - 1)) 
        { // enter filename string
            fileName[fileNameIndex] = cpuData;
            fileNameIndex++;
        }
    }
}

#endif //FILESYSTEM_H
